duanestorey/hifi-amp-pcbs/pcbs/_ready/lift/readme.md

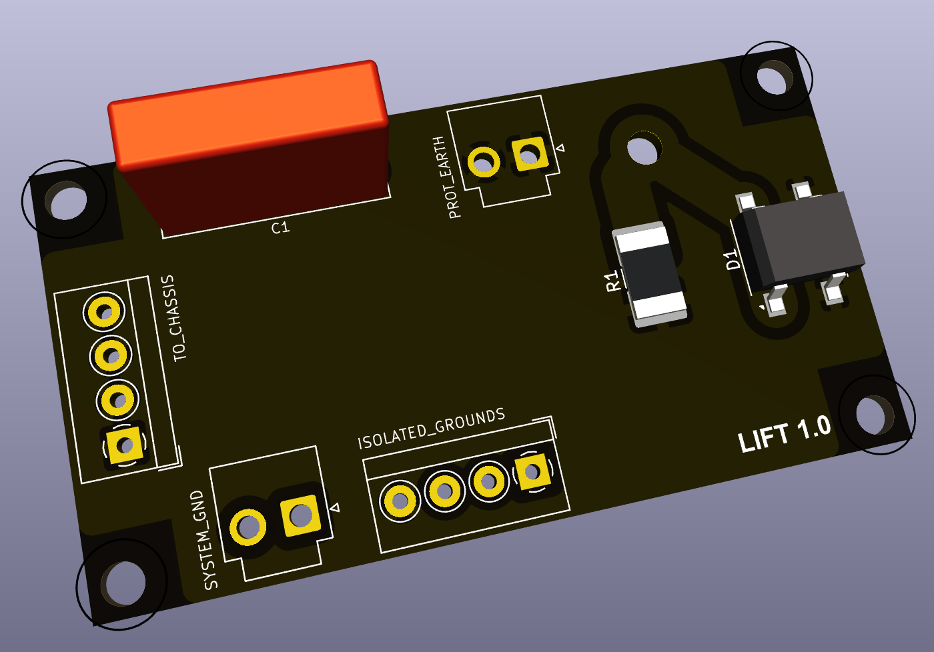
[picture p11: pcbs/_Ready/Lift/screenshot.png]


## Ground Lift

This board provides a ground-lift circuit to isolate the audio grounds from the chassis ground.  May not be legal in some juridictions, but should be safe.

### Version History

- 1.0: Initial Release

### Speciality Components
