duanestorey/hifi-amp-pcbs/pcbs/_ready/lift/1.0/lift.kicad_pcb

## KiCad design pcbs/_ready/lift/1.0/lift.kicad_pcb (2025-01-12)

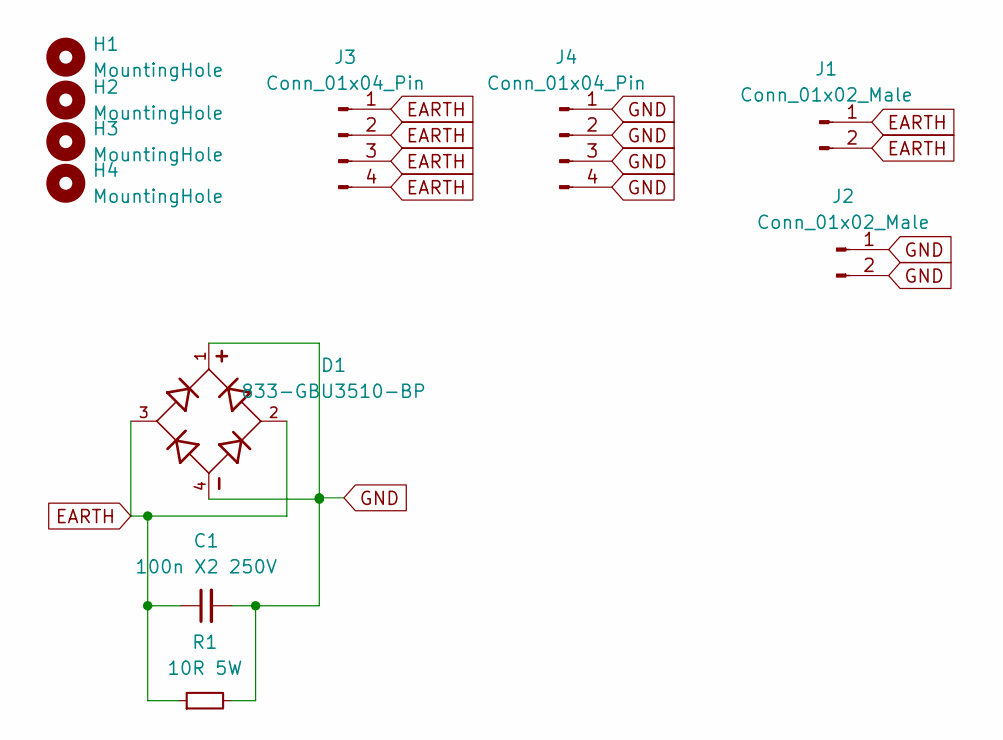
[picture p44: schematic lift.kicad_sch]

Parts:
C1: 100n X2 250V; C_Rect_L18.0mm_W5.0mm_P15.00mm_FKS3_FKP3; Mouser 871-B32922X2104K000
D1: 833-GBU3510-BP; Diode_Bridge_Vishay_GBU; Mouser 833-GBU3510-BP
H1, H2, H3, H4: MountingHole; MountingHole_3.2mm_M3_DIN965_Pad_TopOnly
J1, J2: Conn_01x02_Male; JST_VH_B2P-VH-B_1x02_P3.96mm_Vertical
J3, J4: Conn_01x04_Pin; TerminalBlock_Phoenix_PT-1,5-4-3.5-H_1x04_P3.50mm_Horizontal
R1: 10R 5W; R_Axial_DIN0617_L17.0mm_D6.0mm_P25.40mm_Horizontal; Mouser 594-AC05W10R00J

Connections:
EARTH: C1.1, D1.2, D1.3, J1.1, J1.2, J3.1, J3.2, J3.3, J3.4, R1.1
GND: C1.2, D1.1, D1.4, J2.1, J2.2, J4.1, J4.2, J4.3, J4.4, R1.2

Board: 2 copper layers, 11 parts (0 on the bottom side), 2 nets, no tracks yet.
