duanestorey/hifi-amp-pcbs/pcbs/_ready/inputs/1.0/inputs.kicad_pcb

## KiCad design pcbs/_ready/inputs/1.0/inputs.kicad_pcb (2025-01-12)

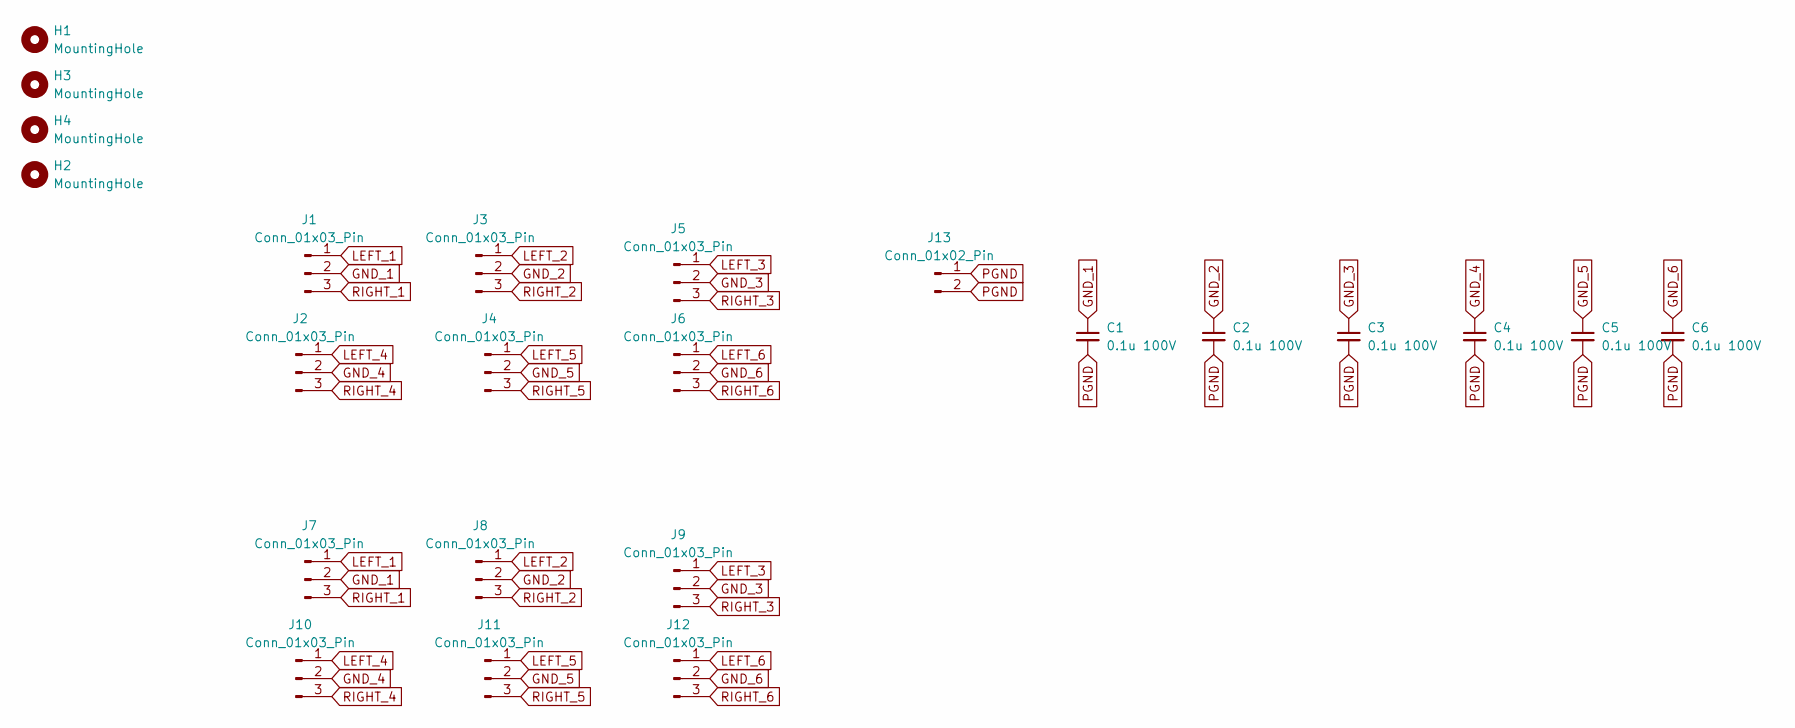
[picture p45: schematic inputs.kicad_sch]

Parts:
C1, C2, C3, C4, C5, C6: 0.1u 100V; C_1206_3216Metric; Mouser 791-1206B104K101CT
H1, H2, H3, H4: MountingHole; MountingHole_3.2mm_M3_DIN965_Pad_TopOnly
J1, J2, J3, J4, J5, J6, J7, J8, J9, J10, J11, J12: Conn_01x03_Pin; JST_PH_B3B-PH-K_1x03_P2.00mm_Vertical
J13: Conn_01x02_Pin; JST_VH_B2P-VH-B_1x02_P3.96mm_Vertical

Connections:
GND_1: C1.1, J1.2, J7.2
GND_2: C2.1, J3.2, J8.2
GND_3: C3.1, J5.2, J9.2
GND_4: C4.1, J2.2, J10.2
GND_5: C5.1, J4.2, J11.2
GND_6: C6.1, J6.2, J12.2
LEFT_1: J1.1, J7.1
LEFT_2: J3.1, J8.1
LEFT_3: J5.1, J9.1
LEFT_4: J2.1, J10.1
LEFT_5: J4.1, J11.1
LEFT_6: J6.1, J12.1
PGND: C1.2, C2.2, C3.2, C4.2, C5.2, C6.2, J13.1, J13.2
RIGHT_1: J1.3, J7.3
RIGHT_2: J3.3, J8.3
RIGHT_3: J5.3, J9.3
RIGHT_4: J2.3, J10.3
RIGHT_5: J4.3, J11.3
RIGHT_6: J6.3, J12.3

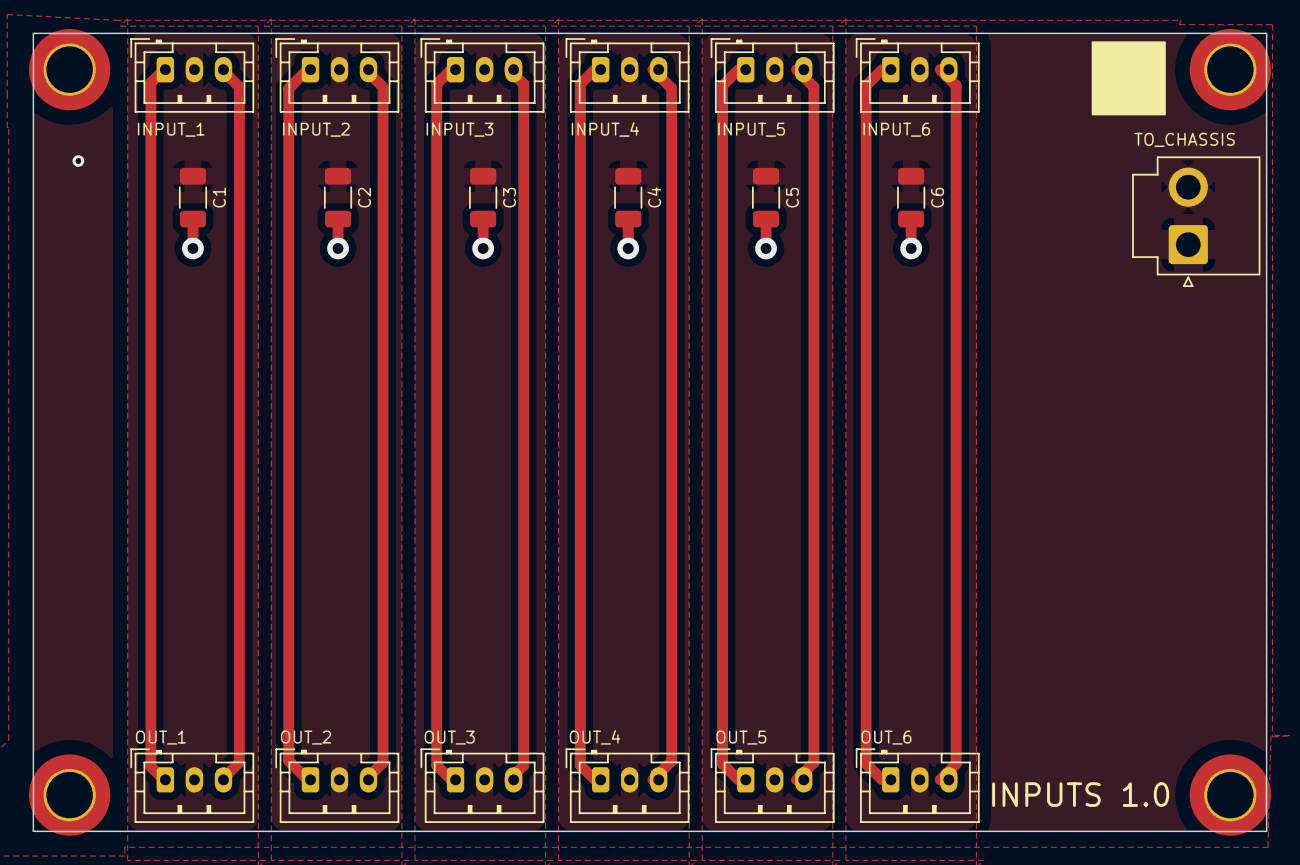
[picture p46: board inputs.kicad_pcb from above]

Board: 2 copper layers, 85.0 x 55.0 mm, 23 parts (0 on the bottom side), 19 nets.
