duanestorey/hifi-amp-pcbs/pcbs/_ready/extend/1.0/extend.kicad_pcb

## KiCad design pcbs/_ready/extend/1.0/extend.kicad_pcb (2025-01-12)

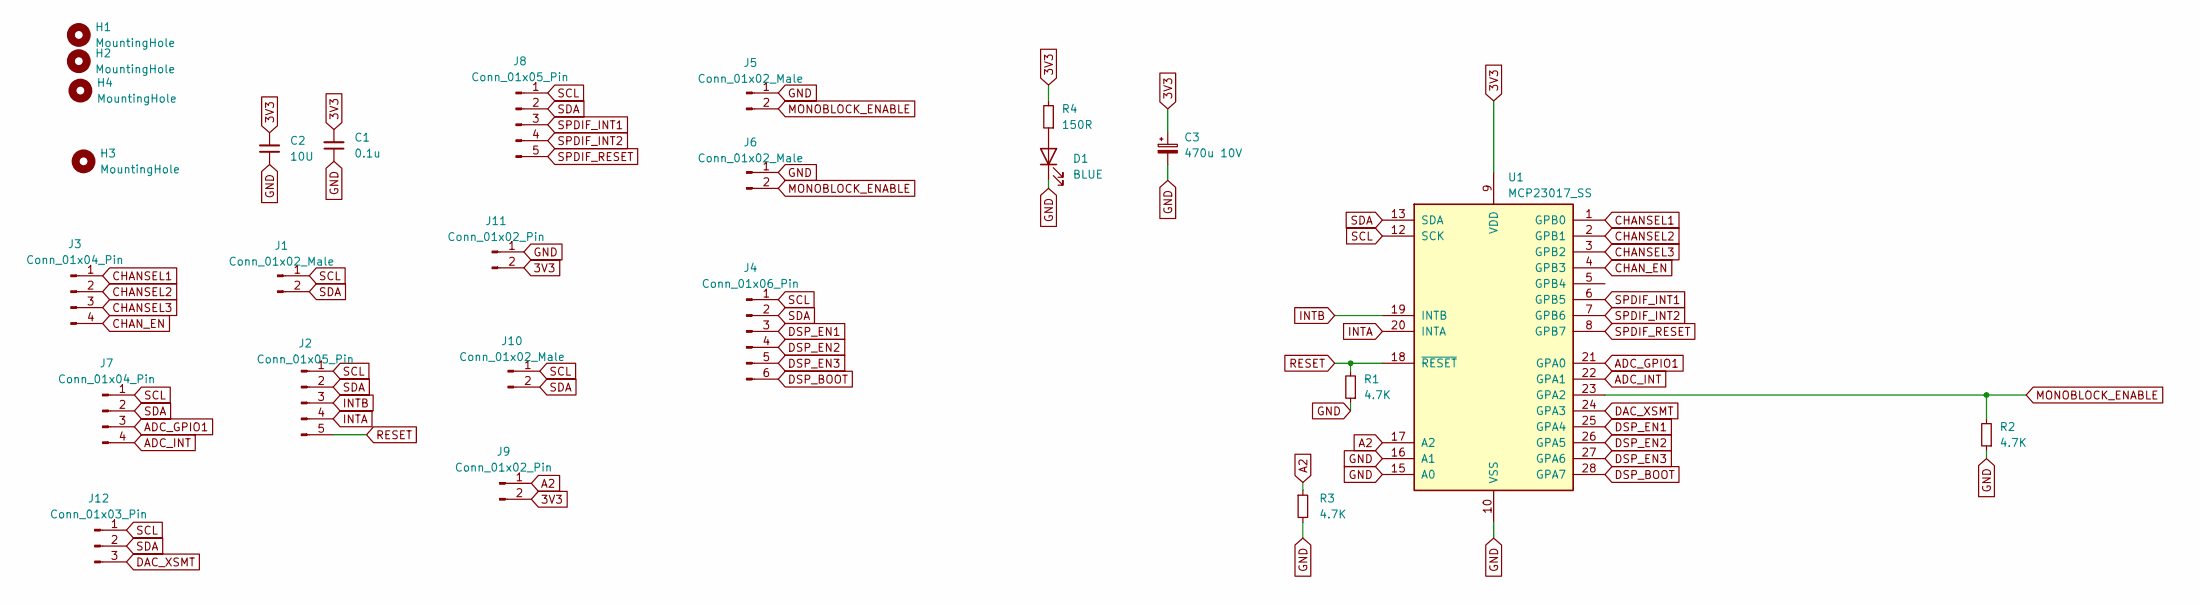
[picture p47: schematic extend.kicad_sch]

Parts:
C1: 0.1u; C_0805_2012Metric_Pad1.18x1.45mm_HandSolder
C2: 10U; C_1206_3216Metric_Pad1.33x1.80mm_HandSolder
C3: 470u 10V; CP_Radial_D6.3mm_P2.50mm
D1: BLUE; LED_0603_1608Metric
H1, H2, H3, H4: MountingHole; MountingHole_3.2mm_M3_DIN965_Pad_TopOnly
J1, J5, J6, J10: Conn_01x02_Male; JST_PH_B2B-PH-K_1x02_P2.00mm_Vertical
J2, J8: Conn_01x05_Pin; JST_PH_B5B-PH-K_1x05_P2.00mm_Vertical
J3, J7: Conn_01x04_Pin; JST_PH_B4B-PH-K_1x04_P2.00mm_Vertical
J4: Conn_01x06_Pin; JST_PH_B6B-PH-K_1x06_P2.00mm_Vertical
J9: Conn_01x02_Pin; PinHeader_1x02_P2.54mm_Vertical
J11: Conn_01x02_Pin; JST_PH_B2B-PH-K_1x02_P2.00mm_Vertical
J12: Conn_01x03_Pin; JST_PH_B3B-PH-K_1x03_P2.00mm_Vertical
R1, R2, R3: 4.7K; R_0603_1608Metric_Pad0.98x0.95mm_HandSolder
R4: 150R; R_0603_1608Metric
U1: MCP23017_SS; SSOP-28_5.3x10.2mm_P0.65mm; Mouser 579-MCP23017-E/SS

Connections:
3V3: C1.2, C2.2, C3.1, J9.2, J11.2, R4.2, U1.9 (VDD)
A2: J9.1, R3.1, U1.17 (A2)
ADC_GPIO1: J7.3, U1.21 (GPA0)
ADC_INT: J7.4, U1.22 (GPA1)
CHANSEL1: J3.1, U1.1 (GPB0)
CHANSEL2: J3.2, U1.2 (GPB1)
CHANSEL3: J3.3, U1.3 (GPB2)
CHAN_EN: J3.4, U1.4 (GPB3)
DAC_XSMT: J12.3, U1.24 (GPA3)
DSP_BOOT: J4.6, U1.28 (GPA7)
DSP_EN1: J4.3, U1.25 (GPA4)
DSP_EN2: J4.4, U1.26 (GPA5)
DSP_EN3: J4.5, U1.27 (GPA6)
GND: C1.1, C2.1, C3.2, D1.1 (K), J5.1, J6.1, J11.1, R1.1, R2.1, R3.2, U1.10 (VSS), U1.15 (A0), U1.16 (A1)
INTA: J2.4, U1.20 (INTA)
INTB: J2.3, U1.19 (INTB)
MONOBLOCK_ENABLE: J5.2, J6.2, R2.2, U1.23 (GPA2)
unnamed: D1.2 (A), R4.1
RESET: J2.5, R1.2, U1.18 (~RESET)
SCL: J1.1, J2.1, J4.1, J7.1, J8.1, J10.1, J12.1, U1.12 (SCK)
SDA: J1.2, J2.2, J4.2, J7.2, J8.2, J10.2, J12.2, U1.13 (SDA)
SPDIF_INT1: J8.3, U1.6 (GPB5)
SPDIF_INT2: J8.4, U1.7 (GPB6)
SPDIF_RESET: J8.5, U1.8 (GPB7)

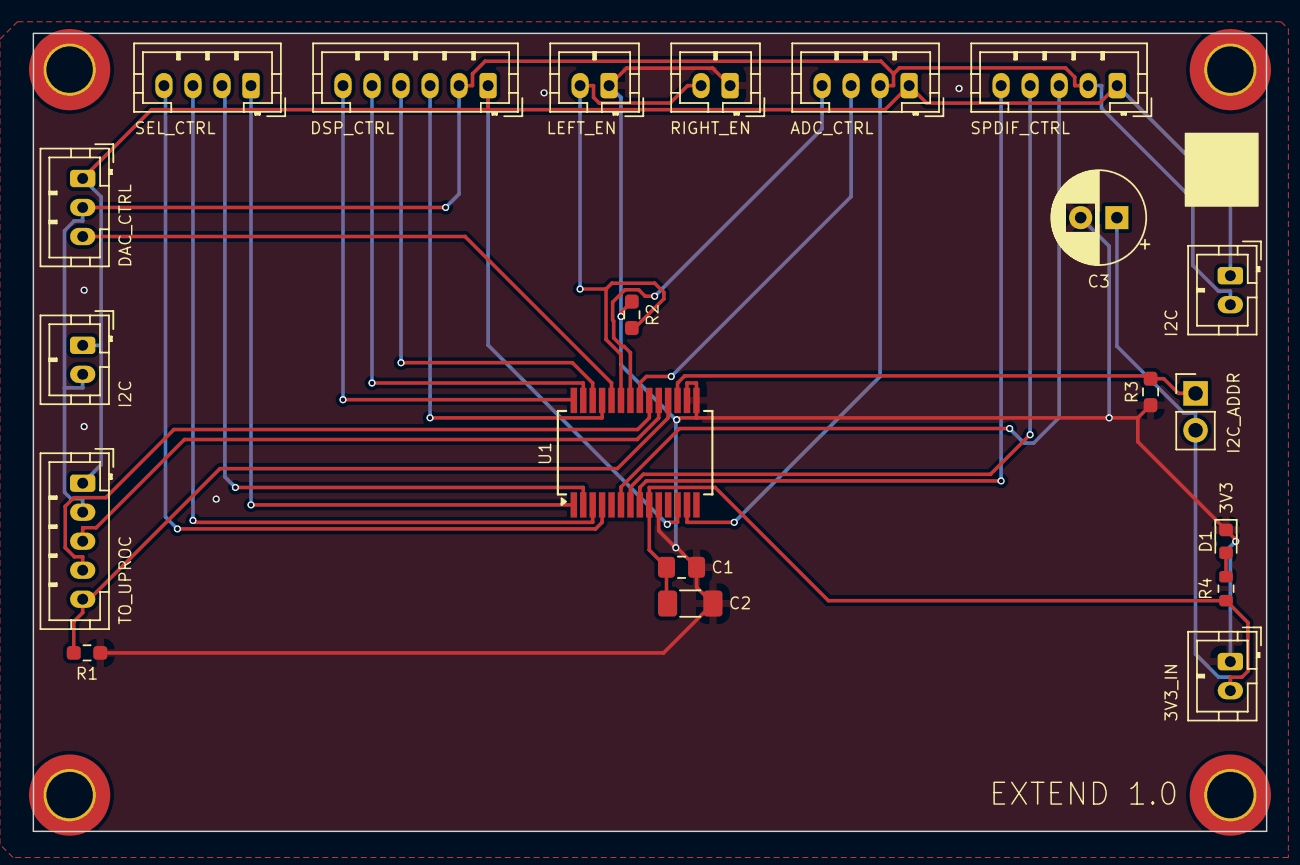
[picture p48: board extend.kicad_pcb from above]

Board: 2 copper layers, 85.0 x 55.0 mm, 25 parts (0 on the bottom side), 24 nets.
