duanestorey/hifi-amp-pcbs/pcbs/_ready/dac/1.0/dac.kicad_pcb

## KiCad design pcbs/_ready/dac/1.0/dac.kicad_pcb (2025-01-12)

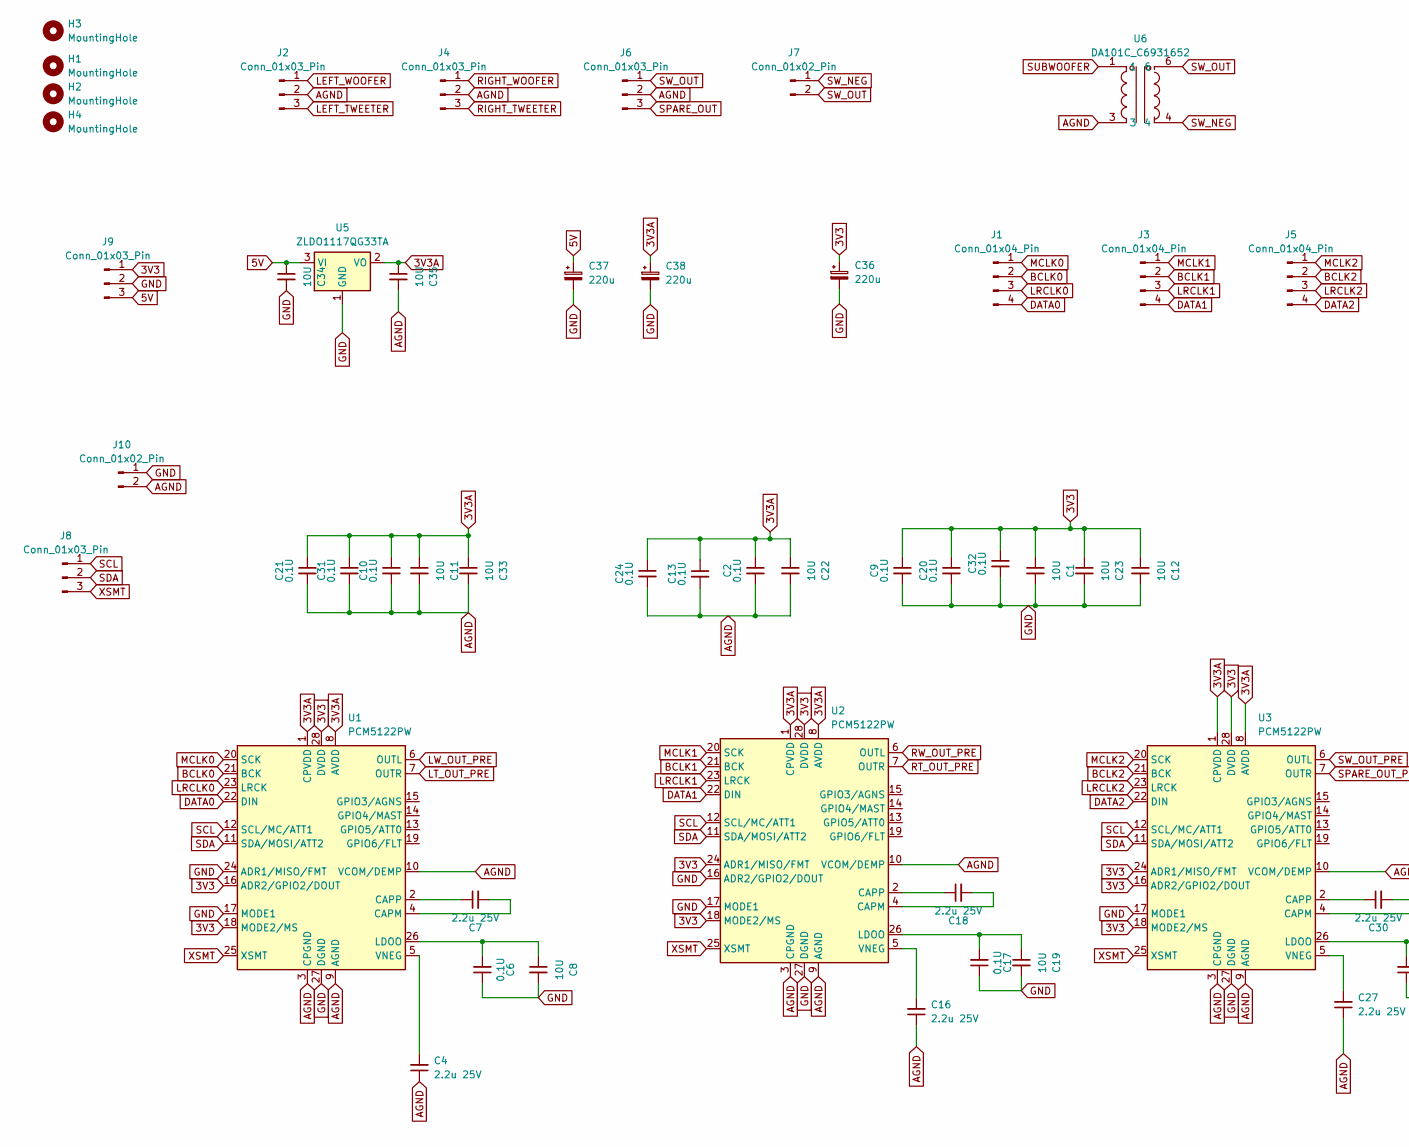
[picture p49: schematic dac.kicad_sch, part in row 1, column 1]

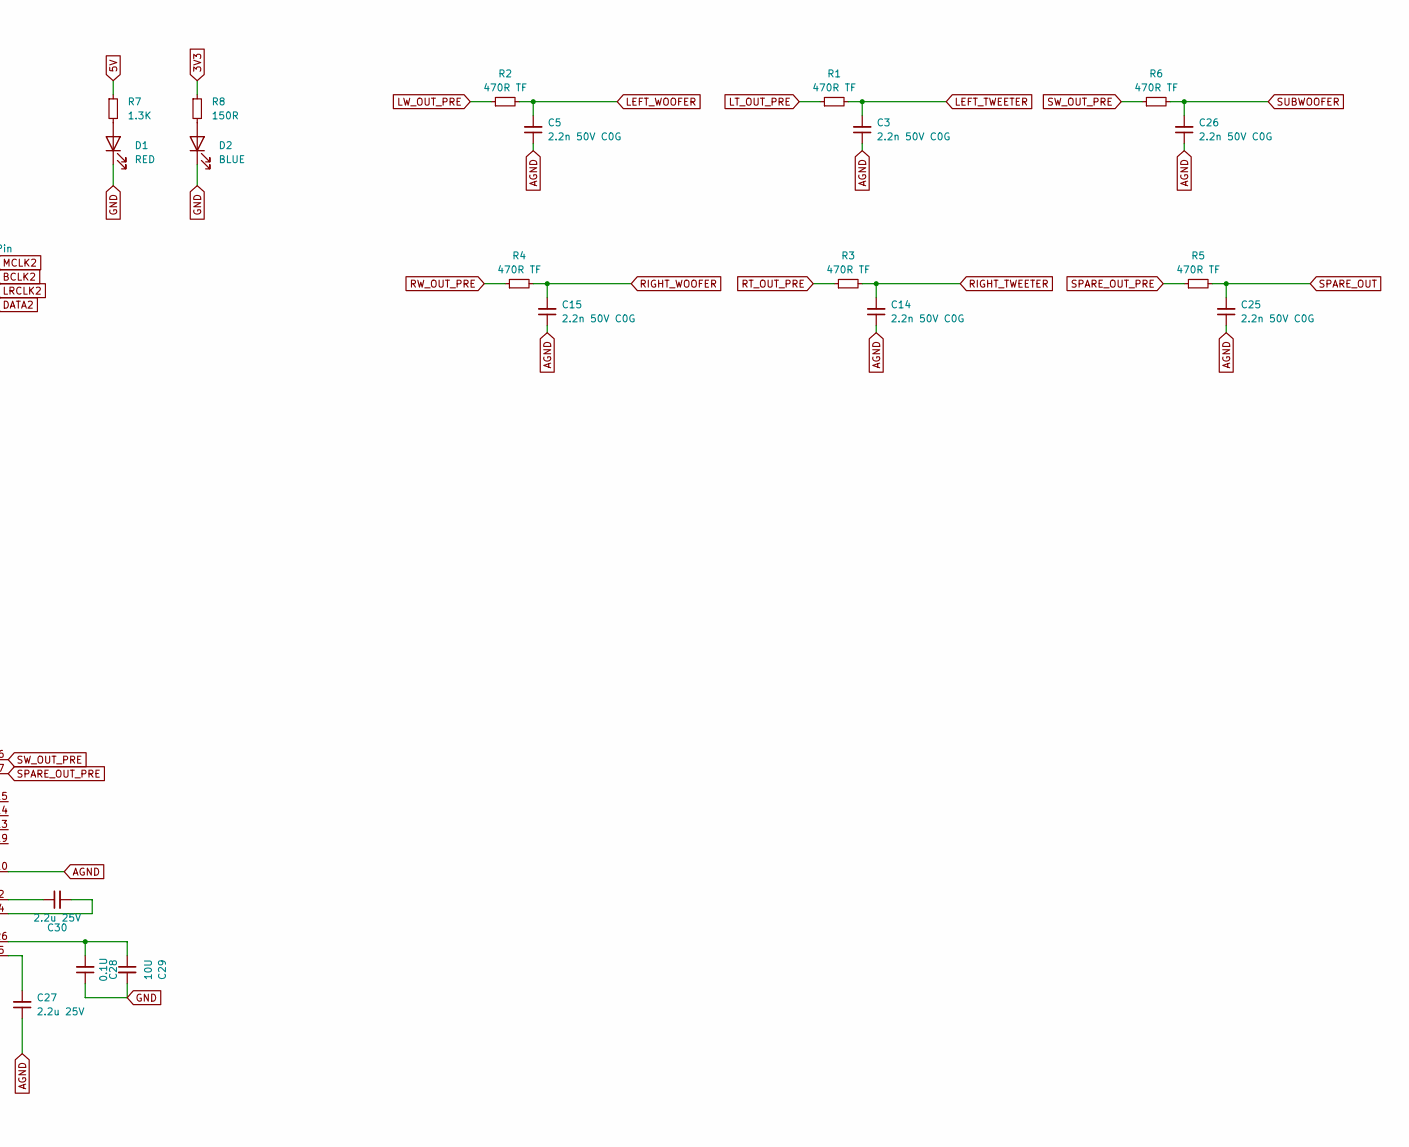
[picture p50: schematic dac.kicad_sch, part in row 1, column 2]

Parts:
C1, C8, C11, C12, C19, C22, C23, C29, C33, C34, C35: 10U; C_1206_3216Metric_Pad1.33x1.80mm_HandSolder
C2, C6, C9, C10, C13, C17, C20, C21, C24, C28, C31, C32: 0.1U; C_0805_2012Metric_Pad1.18x1.45mm_HandSolder
C3, C5, C14, C15: 2.2n 50V C0G; C_0805_2012Metric_Pad1.18x1.45mm_HandSolder; Mouser 791-0805N222F500CT
C4, C16, C27: 2.2u 25V; C_1206_3216Metric_Pad1.33x1.80mm_HandSolder; Mouser 603-CC1206JKX78BB225
C7, C18, C30: 2.2u 25V; C_0805_2012Metric_Pad1.18x1.45mm_HandSolder; Mouser 603-CC1206JKX78BB225
C25, C26: 2.2n 50V C0G; C_0805_2012Metric_Pad1.18x1.45mm_HandSolder
C36, C37, C38: 220u; CP_Radial_D6.3mm_P2.50mm
D1: RED; LED_0603_1608Metric
D2: BLUE; LED_0603_1608Metric
H1, H2, H3, H4: MountingHole; MountingHole_3.2mm_M3_DIN965_Pad_TopOnly
J1, J3, J5: Conn_01x04_Pin; JST_PH_B4B-PH-K_1x04_P2.00mm_Vertical
J2, J4, J6, J8, J9: Conn_01x03_Pin; JST_PH_B3B-PH-K_1x03_P2.00mm_Vertical
J7: Conn_01x02_Pin; JST_PH_B2B-PH-K_1x02_P2.00mm_Vertical
J10: Conn_01x02_Pin; PinHeader_1x02_P2.54mm_Vertical
R1, R2, R3, R4, R5, R6: 470R TF; R_0805_2012Metric_Pad1.20x1.40mm_HandSolder; Mouser 603-RT0805FRE07470RL
R7: 1.3K; R_0603_1608Metric_Pad0.98x0.95mm_HandSolder
R8: 150R; R_0603_1608Metric_Pad0.98x0.95mm_HandSolder
U1, U2, U3: PCM5122PW; TSSOP-28_4.4x9.7mm_P0.65mm; Mouser 595-PCM5122PWR
U5: ZLDO1117QG33TA; SOT-223-3_TabPin2
U6: DA101C_C6931652; XFMR-TH_4P-L9.5-W9.0-P5.08-LS10.2_C9900096976; LCSC Part C6931652

Connections:
3V3: C1.1, C9.1, C12.1, C20.1, C23.1, C32.1, C36.1, J9.1, R8.1, U1.16 (ADR2/GPIO2/DOUT), U1.18 (MODE2/MS), U1.28 (DVDD), U2.18 (MODE2/MS), U2.24 (ADR1/MISO/FMT), U2.28 (DVDD), U3.16 (ADR2/GPIO2/DOUT), U3.18 (MODE2/MS), U3.24 (ADR1/MISO/FMT), U3.28 (DVDD)
3V3A: C2.1, C10.1, C11.1, C13.1, C21.1, C22.1, C24.1, C31.1, C33.1, C35.1, C38.1, U1.1 (CPVDD), U1.8 (AVDD), U2.1 (CPVDD), U2.8 (AVDD), U3.1 (CPVDD), U3.8 (AVDD), U5.2 (VO)
5V: C34.1, C37.1, J9.3, R7.1, U5.3 (VI)
AGND: C2.2, C3.1, C4.1, C5.1, C10.2, C11.2, C13.2, C14.1, C15.1, C16.1, C21.2, C22.2, C24.2, C25.1, C26.1, C27.1, C31.2, C33.2, C35.2, J2.2, J4.2, J6.2, J10.2, U1.3 (CPGND), U1.9 (AGND), U1.10 (VCOM/DEMP), U2.3 (CPGND), U2.9 (AGND), U2.10 (VCOM/DEMP), U3.3 (CPGND), U3.9 (AGND), U3.10 (VCOM/DEMP), U6.3
BCLK0: J1.2, U1.21 (BCK)
BCLK1: J3.2, U2.21 (BCK)
BCLK2: J5.2, U3.21 (BCK)
DATA0: J1.4, U1.22 (DIN)
DATA1: J3.4, U2.22 (DIN)
DATA2: J5.4, U3.22 (DIN)
GND: C1.2, C6.1, C8.2, C9.2, C12.2, C17.1, C19.2, C20.2, C23.2, C28.1, C29.2, C32.2, C34.2, C36.2, C37.2, C38.2, D1.1 (K), D2.1 (K), J9.2, J10.1, U1.17 (MODE1), U1.24 (ADR1/MISO/FMT), U1.27 (DGND), U2.16 (ADR2/GPIO2/DOUT), U2.17 (MODE1), U2.27 (DGND), U3.17 (MODE1), U3.27 (DGND), U5.1 (GND)
LEFT_TWEETER: C3.2, J2.3, R1.2
LEFT_WOOFER: C5.2, J2.1, R2.2
LRCLK0: J1.3, U1.23 (LRCK)
LRCLK1: J3.3, U2.23 (LRCK)
LRCLK2: J5.3, U3.23 (LRCK)
LT_OUT_PRE: R1.1, U1.7 (OUTR)
LW_OUT_PRE: R2.1, U1.6 (OUTL)
MCLK0: J1.1, U1.20 (SCK)
MCLK1: J3.1, U2.20 (SCK)
MCLK2: J5.1, U3.20 (SCK)
unnamed: D1.2 (A), R7.2
unnamed: D2.2 (A), R8.2
unnamed: C7.2, U1.4 (CAPM)
unnamed: C7.1, U1.2 (CAPP)
unnamed: C6.2, C8.1, U1.26 (LDOO)
unnamed: C4.2, U1.5 (VNEG)
unnamed: C18.2, U2.4 (CAPM)
unnamed: C18.1, U2.2 (CAPP)
unnamed: C17.2, C19.1, U2.26 (LDOO)
unnamed: C16.2, U2.5 (VNEG)
unnamed: C30.2, U3.4 (CAPM)
unnamed: C30.1, U3.2 (CAPP)
unnamed: C28.2, C29.1, U3.26 (LDOO)
unnamed: C27.2, U3.5 (VNEG)
RIGHT_TWEETER: C14.2, J4.3, R3.2
RIGHT_WOOFER: C15.2, J4.1, R4.2
RT_OUT_PRE: R3.1, U2.7 (OUTR)
RW_OUT_PRE: R4.1, U2.6 (OUTL)
SCL: J8.1, U1.12 (SCL/MC/ATT1), U2.12 (SCL/MC/ATT1), U3.12 (SCL/MC/ATT1)
SDA: J8.2, U1.11 (SDA/MOSI/ATT2), U2.11 (SDA/MOSI/ATT2), U3.11 (SDA/MOSI/ATT2)
SPARE_OUT: C25.2, J6.3, R5.2
SPARE_OUT_PRE: R5.1, U3.7 (OUTR)
SUBWOOFER: C26.2, R6.2, U6.1
SW_NEG: J7.1, U6.4
SW_OUT: J6.1, J7.2, U6.6
SW_OUT_PRE: R6.1, U3.6 (OUTL)
XSMT: J8.3, U1.25 (XSMT), U2.25 (XSMT), U3.25 (XSMT)

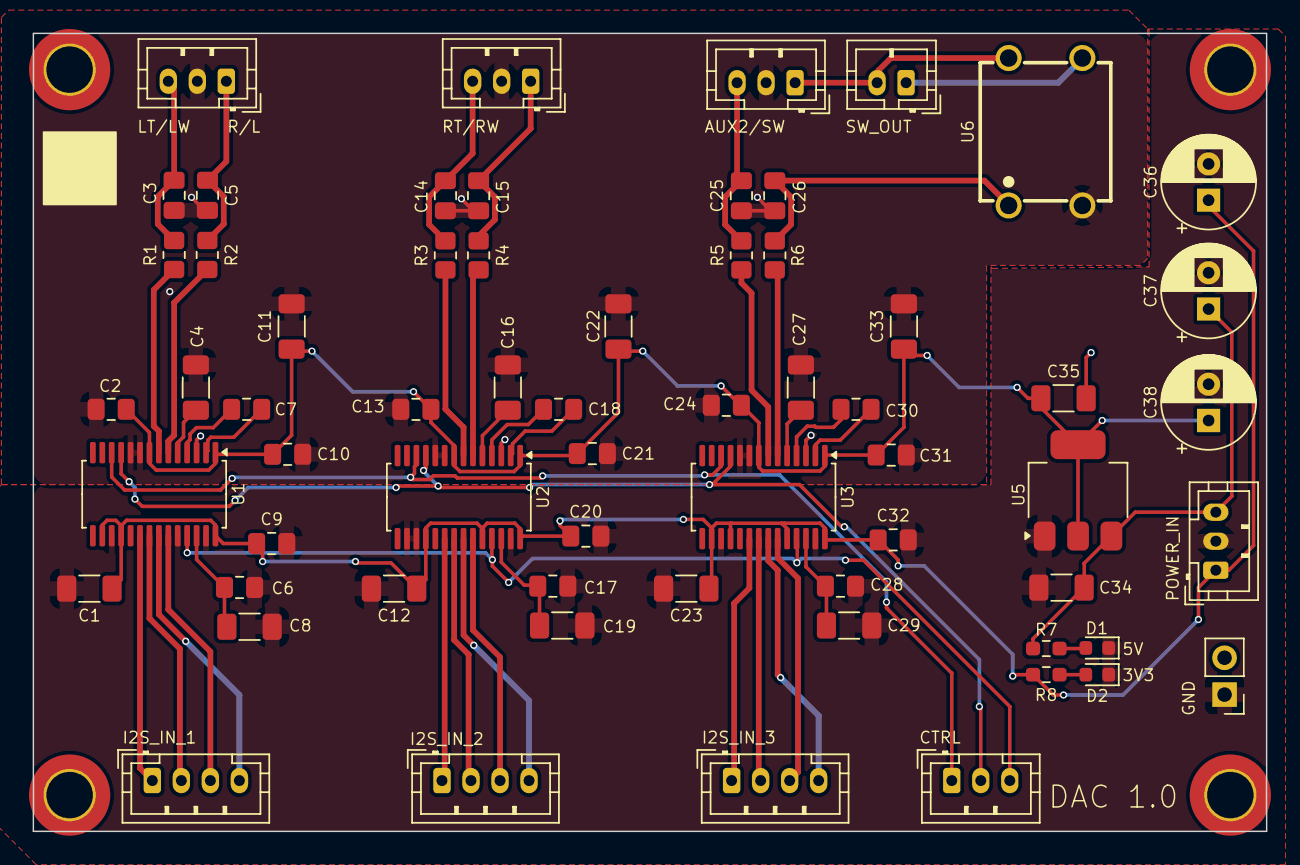
[picture p51: board dac.kicad_pcb from above]

Board: 2 copper layers, 85.0 x 55.0 mm, 67 parts (0 on the bottom side), 48 nets.
