duanestorey/hifi-amp-pcbs/pcbs/_ready/dsp/1.0/dsp.kicad_pcb

## KiCad design pcbs/_ready/dsp/1.0/dsp.kicad_pcb (2025-01-12)

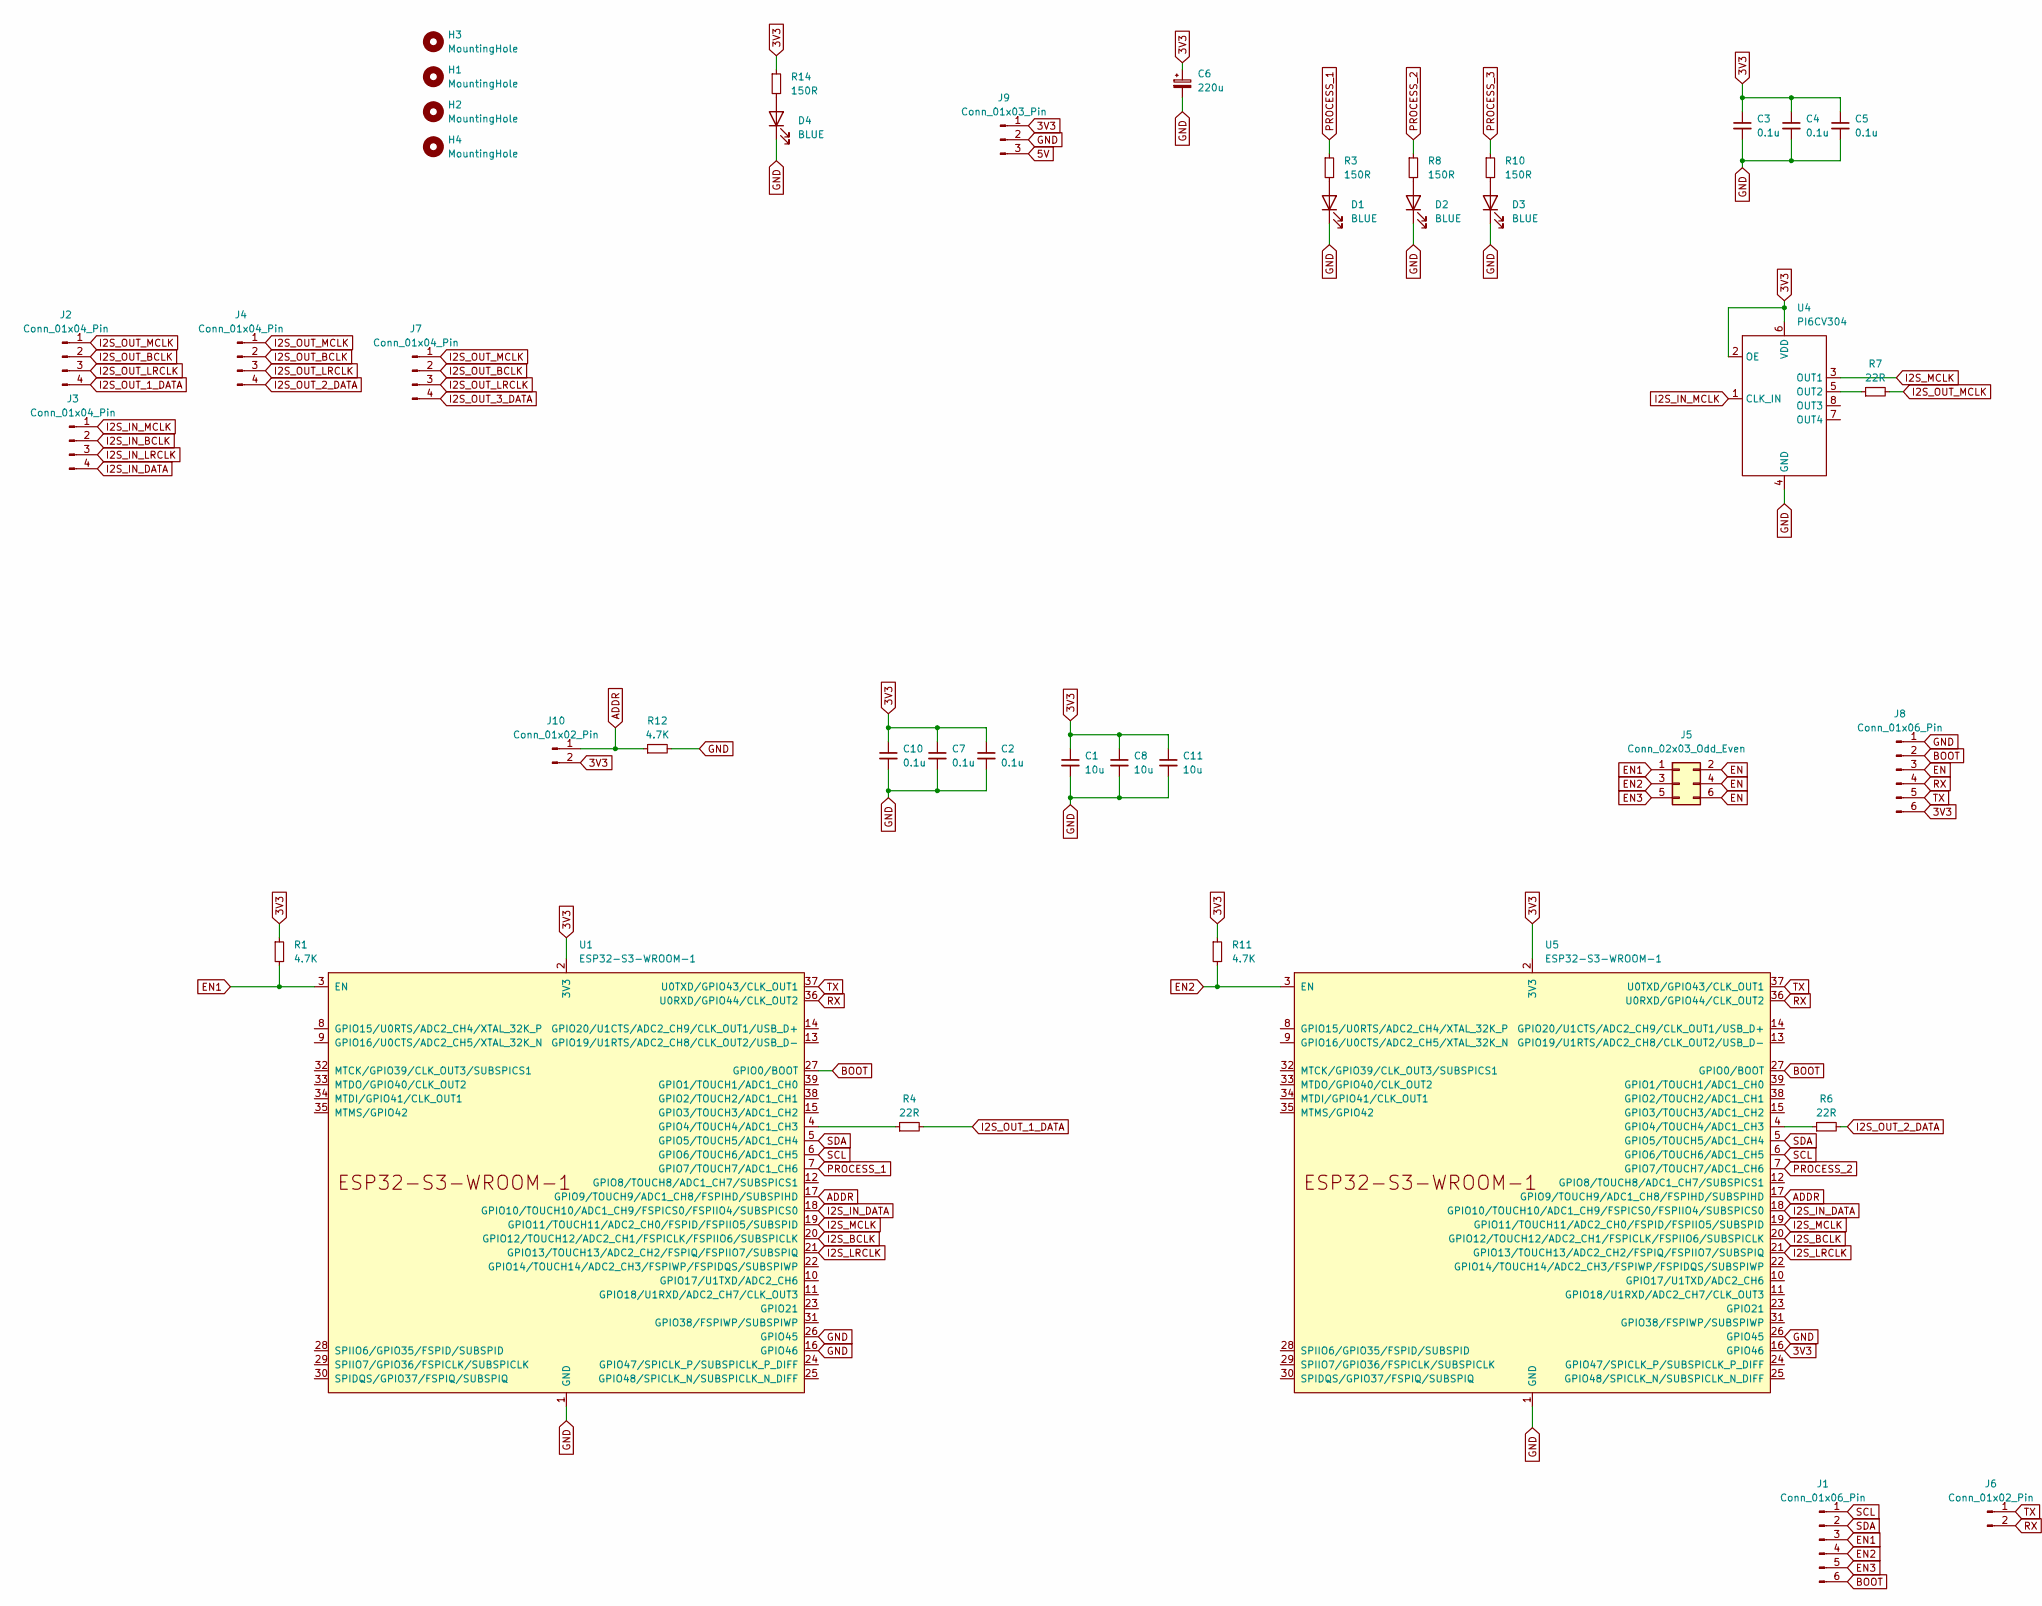
[picture p52: schematic dsp.kicad_sch, part in row 1, column 1]

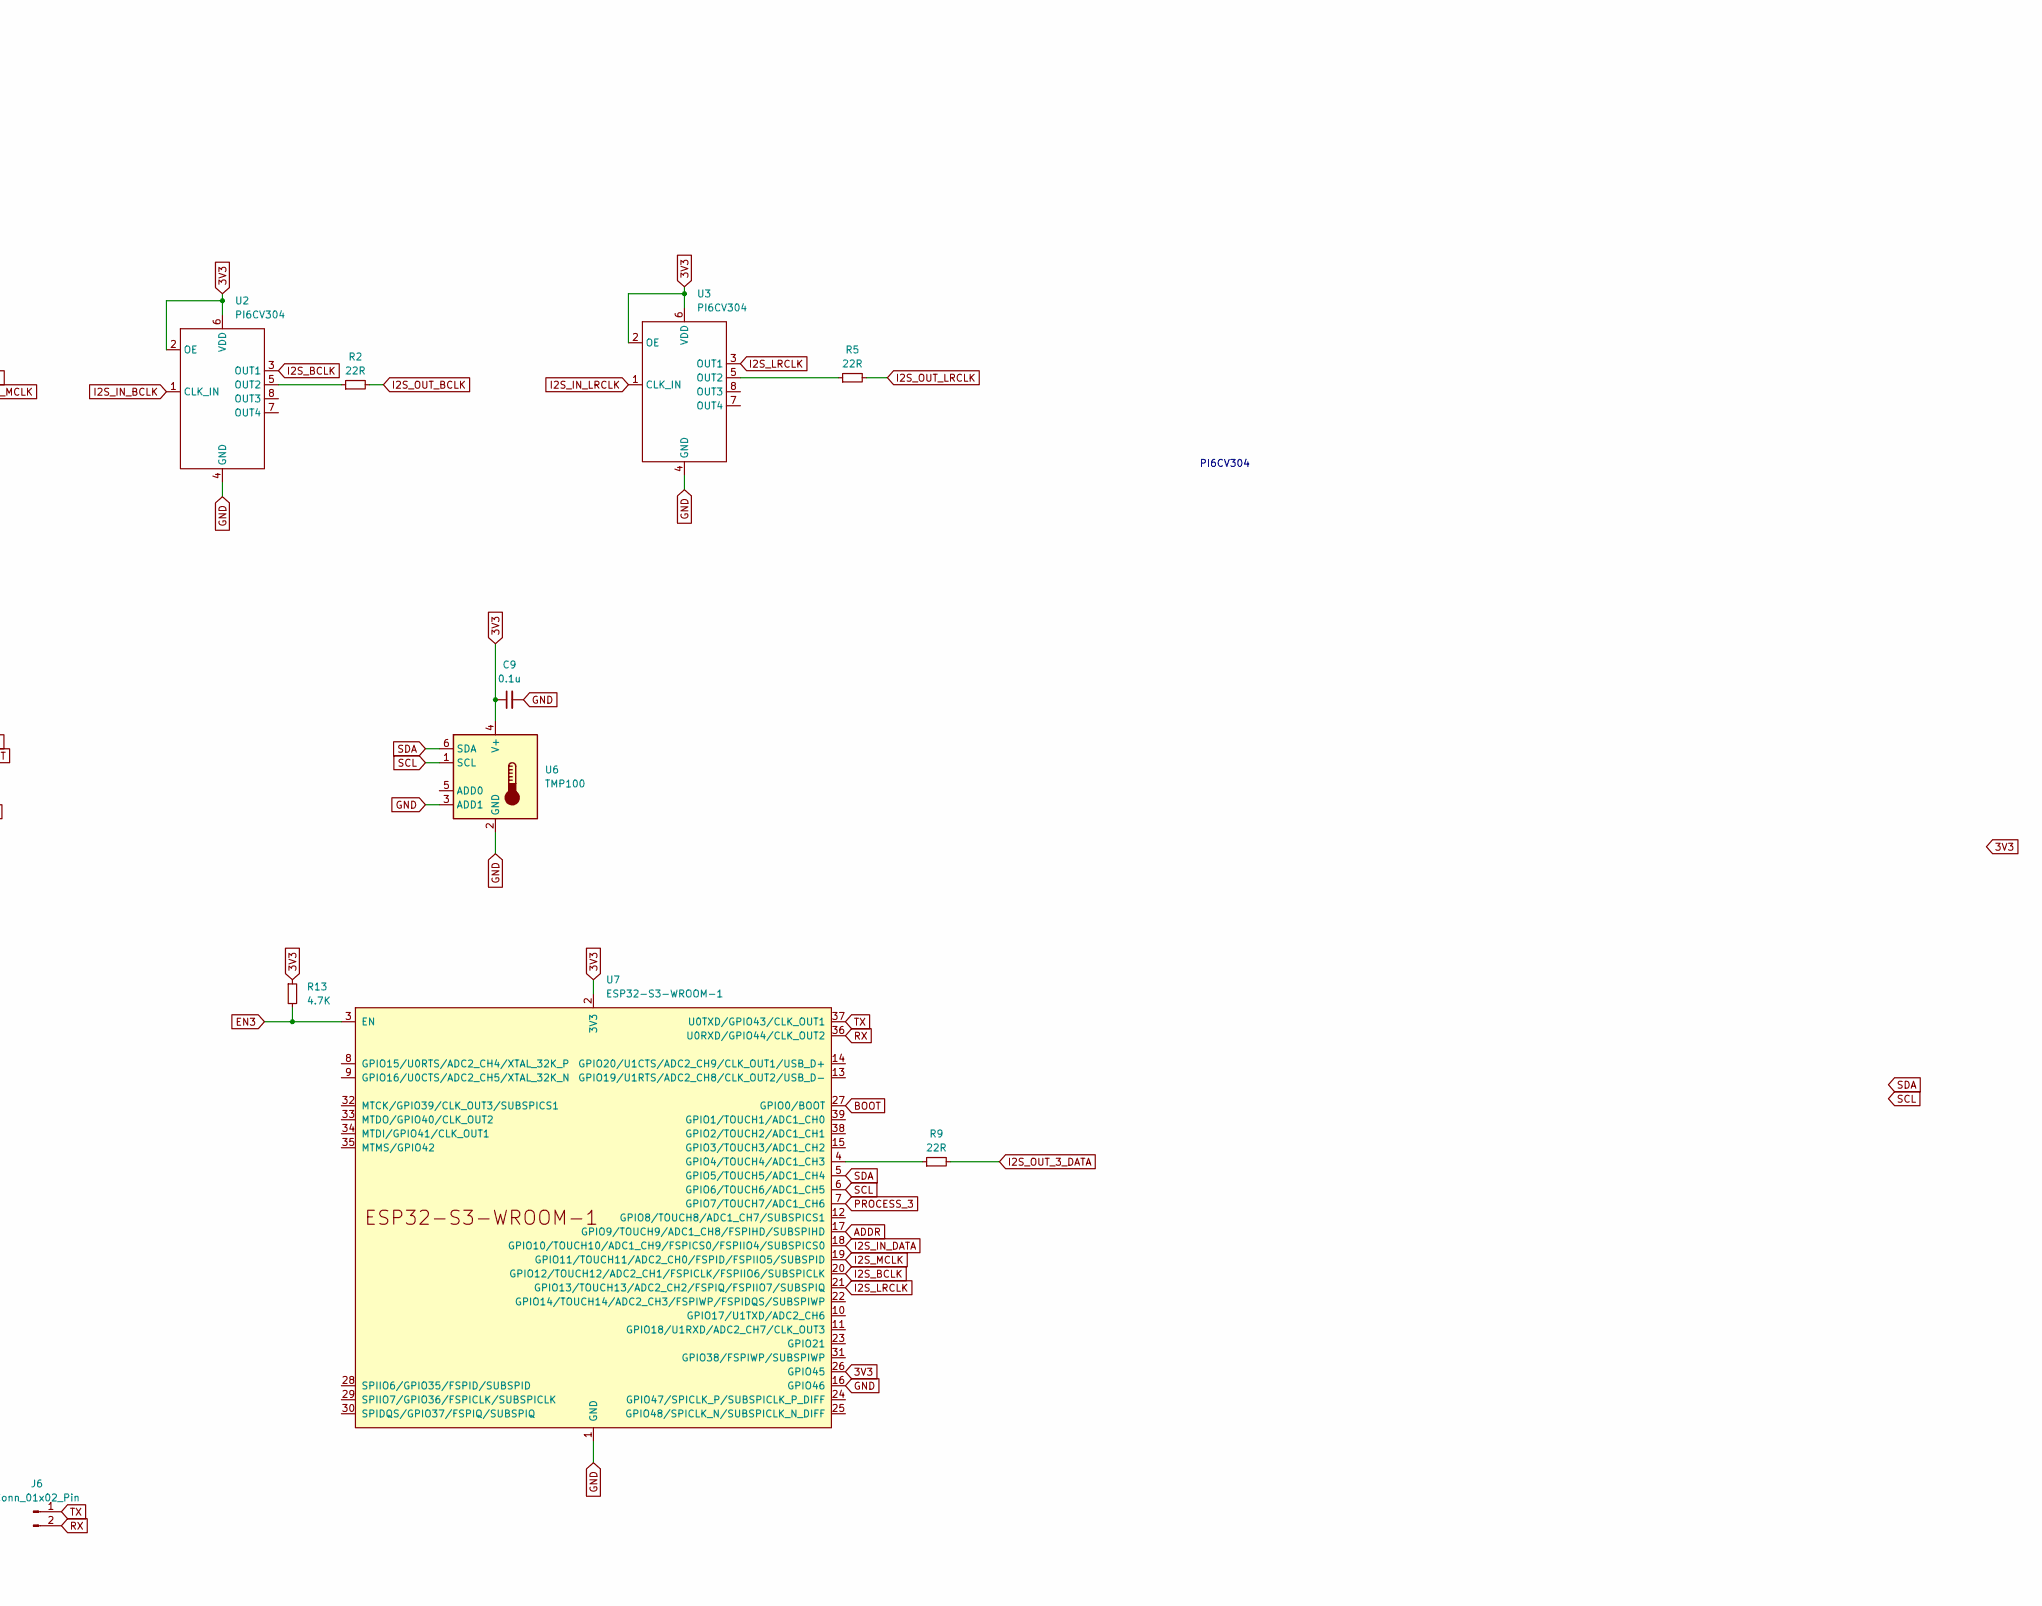
[picture p53: schematic dsp.kicad_sch, part in row 1, column 2]

Parts:
C1, C8, C11: 10u; C_0805_2012Metric_Pad1.18x1.45mm_HandSolder
C2, C3, C4, C5, C7, C9, C10: 0.1u; C_0603_1608Metric_Pad1.08x0.95mm_HandSolder
C6: 220u; CP_Radial_D6.3mm_P2.50mm; LCSC C4747974
D1, D2, D3, D4: BLUE; D_0603_1608Metric; LCSC C84259
H1, H2, H3, H4: MountingHole; MountingHole_3.2mm_M3_DIN965_Pad_TopOnly
J1: Conn_01x06_Pin; JST_PH_B6B-PH-K_1x06_P2.00mm_Vertical
J2, J3, J4, J7: Conn_01x04_Pin; JST_PH_B4B-PH-K_1x04_P2.00mm_Vertical
J5: Conn_02x03_Odd_Even; PinHeader_2x03_P2.54mm_Vertical
J6: Conn_01x02_Pin; JST_PH_B2B-PH-K_1x02_P2.00mm_Vertical
J8: Conn_01x06_Pin; PinHeader_1x06_P2.54mm_Vertical
J9: Conn_01x03_Pin; JST_PH_B3B-PH-K_1x03_P2.00mm_Vertical
J10: Conn_01x02_Pin; PinHeader_1x02_P2.54mm_Vertical
R1, R11, R12, R13: 4.7K; R_0603_1608Metric; LCSC C23162
R2, R5, R7: 22R; R_0603_1608Metric
R3, R8, R10, R14: 150R; R_0603_1608Metric; LCSC C22808
R4, R9: 22R; R_0805_2012Metric; Mouser 603-RT0805FRE0722RL
R6: 22R; R_0805_2012Metric
U1, U5, U7: ESP32-S3-WROOM-1; Mouser 356-ESP32S3WRM1N16R8
U2, U3, U4: PI6CV304; TSSOP-8_4.4x3mm_P0.65mm
U6: TMP100; SOT-23-6

Connections:
3V3: C1.1, C2.1, C3.1, C4.1, C5.1, C6.1, C7.1, C8.1, C9.1, C10.1, C11.1, J8.6, J9.1, J10.2, R1.1, R11.1, R13.1, R14.1, U1.2 (3V3), U2.2 (OE), U2.6 (VDD), U3.2 (OE), U3.6 (VDD), U4.2 (OE), U4.6 (VDD), U5.2 (3V3), U5.16 (GPIO46), U6.4 (V+), U7.2 (3V3), U7.26 (GPIO45)
5V: J9.3
ADDR: J10.1, R12.1, U1.17 (GPIO9/TOUCH9/ADC1_CH8/FSPIHD/SUBSPIHD), U5.17 (GPIO9/TOUCH9/ADC1_CH8/FSPIHD/SUBSPIHD), U7.17 (GPIO9/TOUCH9/ADC1_CH8/FSPIHD/SUBSPIHD)
BOOT: J1.6, J8.2, U1.27 (GPIO0/BOOT), U5.27 (GPIO0/BOOT), U7.27 (GPIO0/BOOT)
EN: J5.2, J5.4, J5.6, J8.3
EN1: J1.3, J5.1, R1.2, U1.3 (EN)
EN2: J1.4, J5.3, R11.2, U5.3 (EN)
EN3: J1.5, J5.5, R13.2, U7.3 (EN)
GND: C1.2, C2.2, C3.2, C4.2, C5.2, C6.2, C7.2, C8.2, C9.2, C10.2, C11.2, D1.1 (K), D2.1 (K), D3.1 (K), D4.1 (K), J8.1, J9.2, R12.2, U1.1 (GND), U1.16 (GPIO46), U1.26 (GPIO45), U1.40 (GND), U1.41 (GND), U2.4 (GND), U3.4 (GND), U4.4 (GND), U5.1 (GND), U5.26 (GPIO45), U5.40 (GND), U5.41 (GND), U6.2 (GND), U6.3 (ADD1), U7.1 (GND), U7.16 (GPIO46), U7.40 (GND), U7.41 (GND)
I2S_BCLK: U1.20 (GPIO12/TOUCH12/ADC2_CH1/FSPICLK/FSPIIO6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), U2.3 (OUT1), U5.20 (GPIO12/TOUCH12/ADC2_CH1/FSPICLK/FSPIIO6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), U7.20 (GPIO12/TOUCH12/ADC2_CH1/FSPICLK/FSPIIO6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)
I2S_IN_BCLK: J3.2, U2.1 (CLK_IN)
I2S_IN_DATA: J3.4, U1.18 (GPIO10/TOUCH10/ADC1_CH9/FSPICS0/FSPIIO4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), U5.18 (GPIO10/TOUCH10/ADC1_CH9/FSPICS0/FSPIIO4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), U7.18 (GPIO10/TOUCH10/ADC1_CH9/FSPICS0/FSPIIO4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)
I2S_IN_LRCLK: J3.3, U3.1 (CLK_IN)
I2S_IN_MCLK: J3.1, U4.1 (CLK_IN)
I2S_LRCLK: U1.21 (GPIO13/TOUCH13/ADC2_CH2/FSPIQ/FSPIIO7/S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), U3.3 (OUT1), U5.21 (GPIO13/TOUCH13/ADC2_CH2/FSPIQ/FSPIIO7/S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), U7.21 (GPIO13/TOUCH13/ADC2_CH2/FSPIQ/FSPIIO7/S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)
I2S_MCLK: U1.19 (GPIO11/TOUCH11/ADC2_CH0/FSPID/FSPIIO5/S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), U4.3 (OUT1), U5.19 (GPIO11/TOUCH11/ADC2_CH0/FSPID/FSPIIO5/S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), U7.19 (GPIO11/TOUCH11/ADC2_CH0/FSPID/FSPIIO5/S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)
I2S_OUT_1_DATA: J2.4, R4.2
I2S_OUT_2_DATA: J4.4, R6.2
I2S_OUT_3_DATA: J7.4, R9.2
I2S_OUT_BCLK: J2.2, J4.2, J7.2, R2.2
I2S_OUT_LRCLK: J2.3, J4.3, J7.3, R5.2
I2S_OUT_MCLK: J2.1, J4.1, J7.1, R7.2
unnamed: D1.2 (A), R3.2
unnamed: D2.2 (A), R8.2
unnamed: D3.2 (A), R10.2
unnamed: D4.2 (A), R14.2
unnamed: R4.1, U1.4 (GPIO4/TOUCH4/ADC1_CH3)
unnamed: R2.1, U2.5 (OUT2)
unnamed: R5.1, U3.5 (OUT2)
unnamed: R7.1, U4.5 (OUT2)
unnamed: R6.1, U5.4 (GPIO4/TOUCH4/ADC1_CH3)
unnamed: R9.1, U7.4 (GPIO4/TOUCH4/ADC1_CH3)
PROCESS_1: R3.1, U1.7 (GPIO7/TOUCH7/ADC1_CH6)
PROCESS_2: R8.1, U5.7 (GPIO7/TOUCH7/ADC1_CH6)
PROCESS_3: R10.1, U7.7 (GPIO7/TOUCH7/ADC1_CH6)
RX: J6.2, J8.4, U1.36 (U0RXD/GPIO44/CLK_OUT2), U5.36 (U0RXD/GPIO44/CLK_OUT2), U7.36 (U0RXD/GPIO44/CLK_OUT2)
SCL: J1.1, U1.6 (GPIO6/TOUCH6/ADC1_CH5), U5.6 (GPIO6/TOUCH6/ADC1_CH5), U6.1 (SCL), U7.6 (GPIO6/TOUCH6/ADC1_CH5)
SDA: J1.2, U1.5 (GPIO5/TOUCH5/ADC1_CH4), U5.5 (GPIO5/TOUCH5/ADC1_CH4), U6.6 (SDA), U7.5 (GPIO5/TOUCH5/ADC1_CH4)
TX: J6.1, J8.5, U1.37 (U0TXD/GPIO43/CLK_OUT1), U5.37 (U0TXD/GPIO43/CLK_OUT1), U7.37 (U0TXD/GPIO43/CLK_OUT1)

Notes on the sheet:
PI6CV304

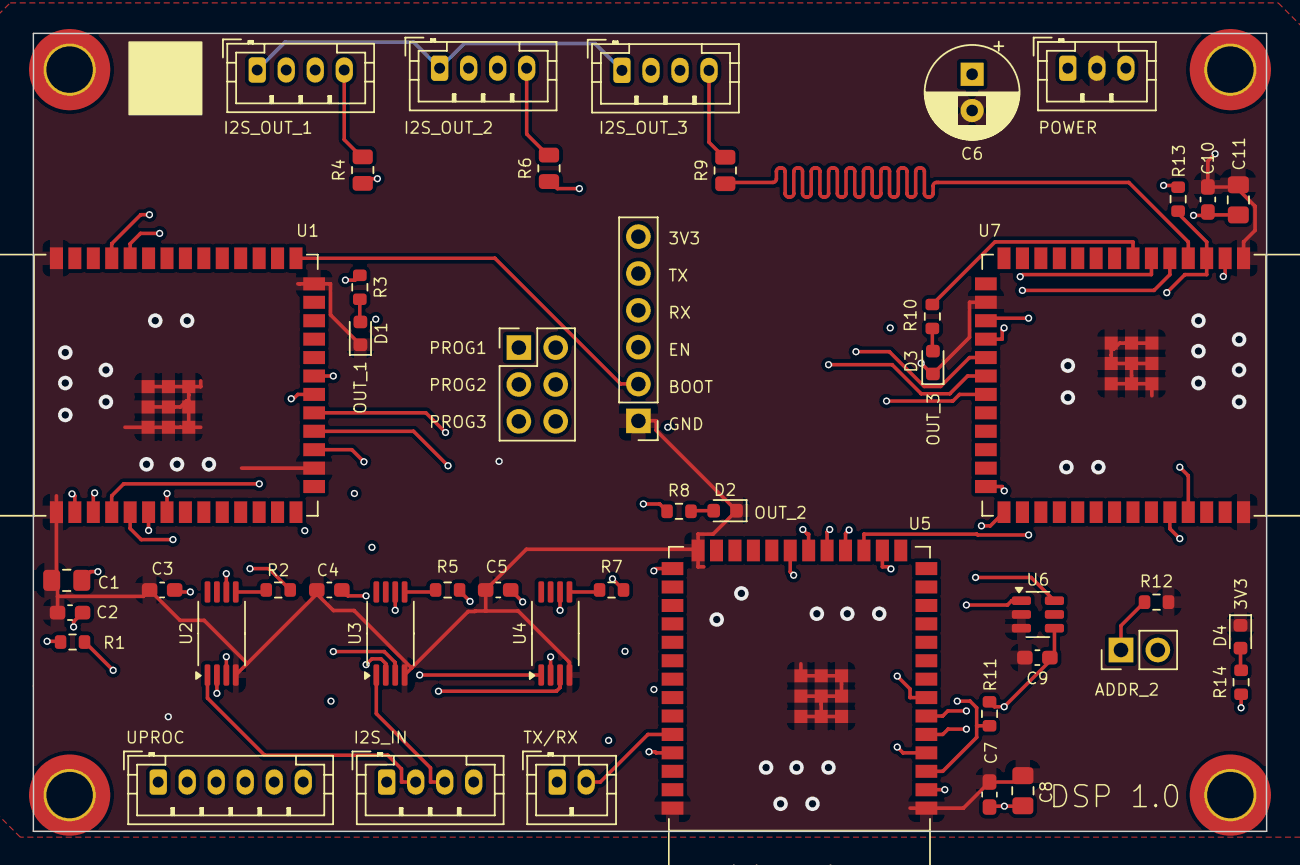
[picture p54: board dsp.kicad_pcb from above]

Board: 4 copper layers, 85.0 x 55.0 mm, 50 parts (0 on the bottom side), 38 nets.
