duanestorey/hifi-amp-pcbs/pcbs/_ready/spdif/_Archived/CS8416/0.1/SPDIF.kicad_pcb

## KiCad design pcbs/_ready/spdif/_Archived/CS8416/0.1/SPDIF.kicad_pcb (2025-01-04, an earlier design)

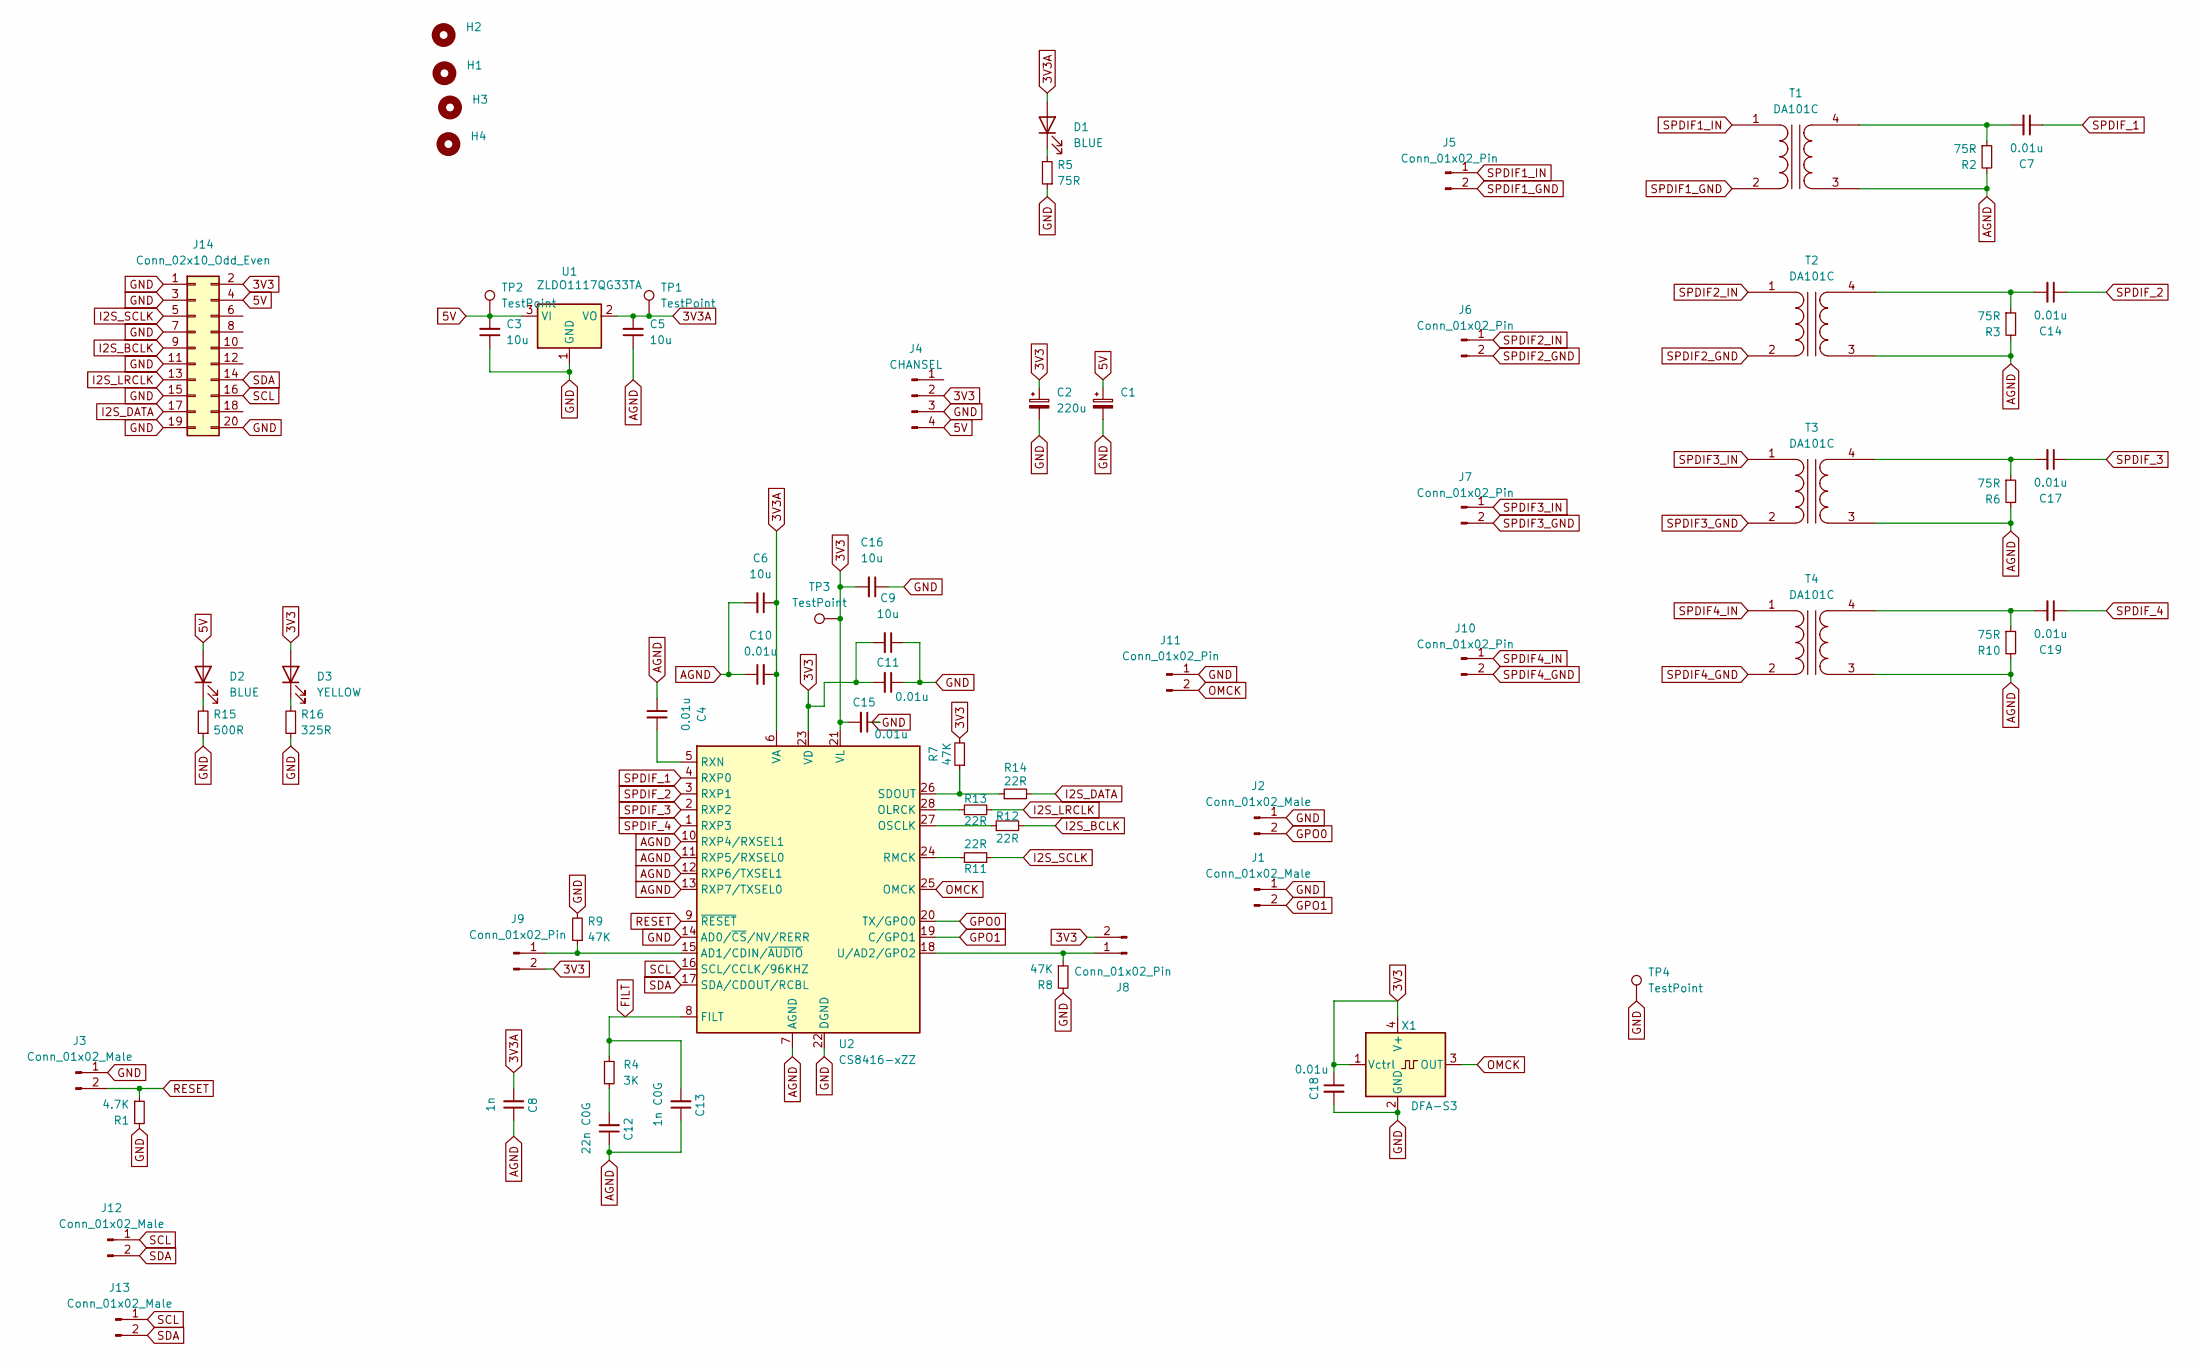
[picture p55: schematic SPDIF.kicad_sch]

Parts:
C1, C2: 220u; CP_Radial_D6.3mm_P2.50mm
C3, C5, C6, C9, C16: 10u; C_1206_3216Metric_Pad1.33x1.80mm_HandSolder
C4, C7, C14, C17, C19: 0.01u; C_0805_2012Metric_Pad1.18x1.45mm_HandSolder
C8: 1n; C_0805_2012Metric_Pad1.18x1.45mm_HandSolder
C10: 0.01u; C_1206_3216Metric_Pad1.33x1.80mm_HandSolder
C11, C15, C18: 0.01u; C_0805_2012Metric
C12: 22n C0G; C_0805_2012Metric_Pad1.18x1.45mm_HandSolder
C13: 1n C0G; C_0805_2012Metric_Pad1.18x1.45mm_HandSolder
D1, D2: BLUE; LED_0805_2012Metric_Pad1.15x1.40mm_HandSolder
D3: YELLOW; LED_0805_2012Metric_Pad1.15x1.40mm_HandSolder
H1, H2, H3, H4: MountingHole; MountingHole_3.2mm_M3
J1, J2, J3, J12, J13: Conn_01x02_Male; JST_PH_B2B-PH-K_1x02_P2.00mm_Vertical
J4: CHANSEL; JST_XH_B4B-XH-A_1x04_P2.50mm_Vertical
J5, J6, J7, J10: Conn_01x02_Pin; JST_XH_B2B-XH-A_1x02_P2.50mm_Vertical
J8, J9, J11: Conn_01x02_Pin; PinHeader_1x02_P2.54mm_Vertical
J14: Conn_02x10_Odd_Even; PinHeader_2x10_P2.54mm_Vertical
R1: 4.7K; R_0603_1608Metric_Pad0.98x0.95mm_HandSolder
R2, R3, R5, R6, R10: 75R; R_0603_1608Metric_Pad0.98x0.95mm_HandSolder
R4: 3K; R_0805_2012Metric_Pad1.20x1.40mm_HandSolder
R7, R8, R9: 47K; R_0603_1608Metric_Pad0.98x0.95mm_HandSolder
R11, R12, R13, R14: 22R; R_1206_3216Metric_Pad1.30x1.75mm_HandSolder
R15: 500R; R_0603_1608Metric_Pad0.98x0.95mm_HandSolder
R16: 325R; R_0603_1608Metric_Pad0.98x0.95mm_HandSolder
T1, T2, T3, T4: DA101C
TP1, TP2, TP3, TP4: TestPoint; TestPoint_THTPad_2.0x2.0mm_Drill1.0mm
U1: ZLDO1117QG33TA; SOT-223-3_TabPin2
U2: CS8416-xZZ; TSSOP-28_4.4x9.7mm_P0.65mm
X1: DFA-S3; Oscillator_SMD_EuroQuartz_XO53-4Pin_5.0x3.2mm_HandSoldering

Connections:
3V3: C2.1, C9.2, C11.2, C15.2, C16.2, C18.1, D3.2 (A), J4.2, J8.2, J9.2, J14.2, R7.2, TP3.1, U2.21 (VL), U2.23 (VD), X1.1 (Vctrl), X1.4 (V+)
3V3A: C5.2, C6.1, C8.2, C10.2, D1.2 (A), TP1.1, U1.2 (VO), U2.6 (VA)
5V: C1.1, C3.2, D2.2 (A), J4.4, J14.4, TP2.1, U1.3 (VI)
AGND: C4.1, C5.1, C6.2, C8.1, C10.1, C12.1, C13.1, R2.2, R3.2, R6.2, R10.2, T1.3 (SA), T2.3 (SA), T3.3 (SA), T4.3 (SA), U2.7 (AGND), U2.10 (RXP4/RXSEL1), U2.11 (RXP5/RXSEL0), U2.12 (RXP6/TXSEL1), U2.13 (RXP7/TXSEL0)
FILT: C13.2, R4.1, U2.8 (FILT)
GND: C1.2, C2.2, C3.1, C9.1, C11.1, C15.1, C16.1, C18.2, J1.1, J2.1, J3.1, J4.3, J11.1, J14.1, J14.3, J14.7, J14.11, J14.15, J14.19, J14.20, R1.2, R5.1, R8.2, R9.2, R15.1, R16.1, TP4.1, U1.1 (GND), U2.14 (AD0/~CS/NV/RERR), U2.22 (DGND), X1.2 (GND)
GPO0: J2.2, U2.20 (TX/GPO0)
GPO1: J1.2, U2.19 (C/GPO1)
I2S_BCLK: J14.9, R12.2
I2S_DATA: J14.17, R14.2
I2S_LRCLK: J14.13, R13.2
I2S_SCLK: J14.5, R11.2
unnamed: C12.2, R4.2
unnamed: D1.1 (K), R5.2
unnamed: D2.1 (K), R15.2
unnamed: D3.1 (K), R16.2
unnamed: J8.1, R8.1, U2.18 (U/AD2/GPO2)
unnamed: J9.1, R9.1, U2.15 (AD1/CDIN/~AUDIO)
unnamed: C7.2, R2.1, T1.4 (SB)
unnamed: C14.2, R3.1, T2.4 (SB)
unnamed: C17.2, R6.1, T3.4 (SB)
unnamed: C19.2, R10.1, T4.4 (SB)
unnamed: R13.1, U2.28 (OLRCK)
unnamed: R12.1, U2.27 (OSCLK)
unnamed: R11.1, U2.24 (RMCK)
unnamed: C4.2, U2.5 (RXN)
unnamed: R7.1, R14.1, U2.26 (SDOUT)
OMCK: J11.2, U2.25 (OMCK), X1.3 (OUT)
RESET: J3.2, R1.1, U2.9 (~RESET)
SCL: J12.1, J13.1, J14.16, U2.16 (SCL/CCLK/96KHZ)
SDA: J12.2, J13.2, J14.14, U2.17 (SDA/CDOUT/RCBL)
SPDIF1_GND: J5.2, T1.2 (AB)
SPDIF1_IN: J5.1, T1.1 (AA)
SPDIF2_GND: J6.2, T2.2 (AB)
SPDIF2_IN: J6.1, T2.1 (AA)
SPDIF3_GND: J7.2, T3.2 (AB)
SPDIF3_IN: J7.1, T3.1 (AA)
SPDIF4_GND: J10.2, T4.2 (AB)
SPDIF4_IN: J10.1, T4.1 (AA)
SPDIF_1: C7.1, U2.4 (RXP0)
SPDIF_2: C14.1, U2.3 (RXP1)
SPDIF_3: C17.1, U2.2 (RXP2)
SPDIF_4: C19.1, U2.1 (RXP3)

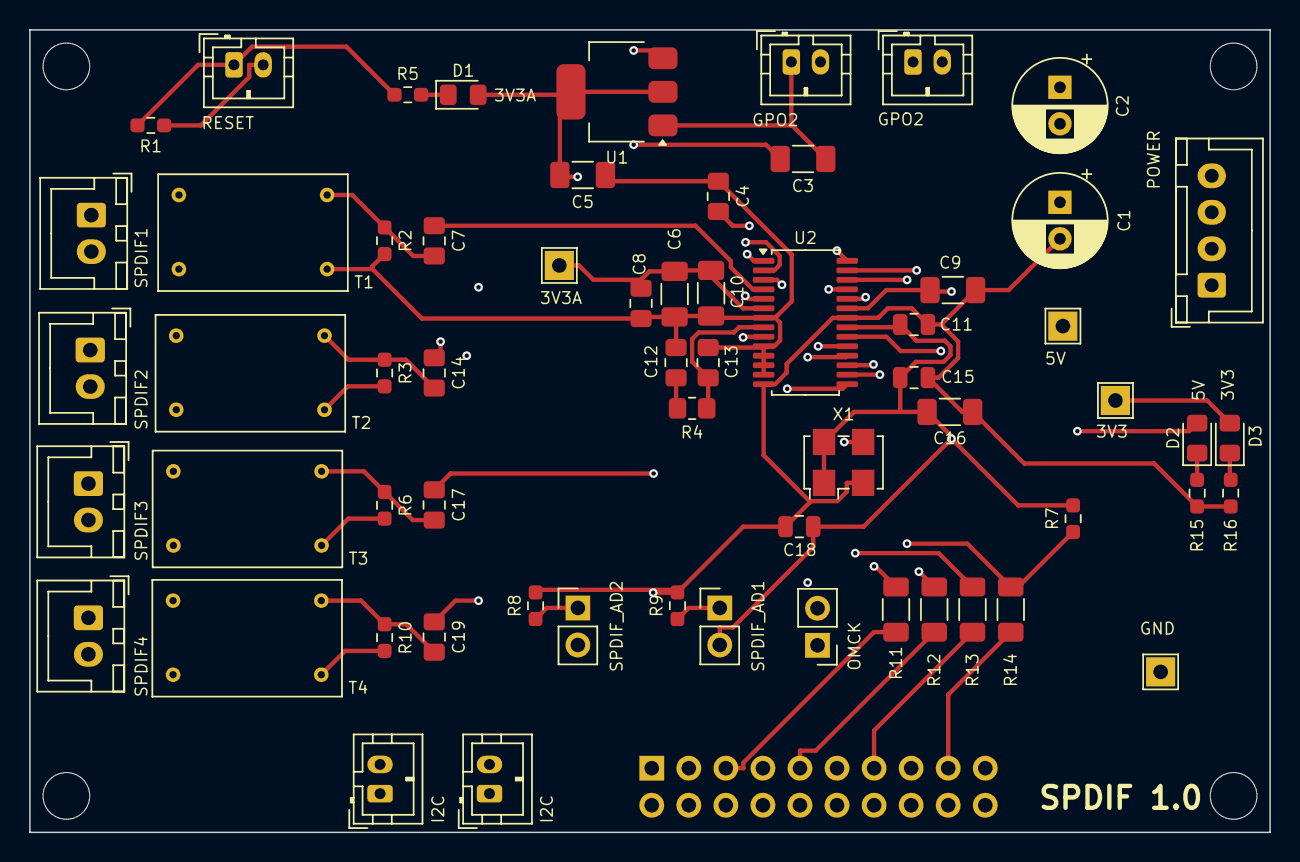
[picture p56: board pcbs/_ready/spdif/_Archived/CS8416/0.1/SPDIF.kicad_pcb from above]

Board: 4 copper layers, 85.0 x 55.0 mm, 67 parts (1 on the bottom side), 43 nets.
