duanestorey/hifi-amp-pcbs/pcbs/_ready/spdif/_Archived/WM8805/0.1/SPDIF.kicad_pcb

## KiCad design pcbs/_ready/spdif/_Archived/WM8805/0.1/SPDIF.kicad_pcb (2025-01-04, an earlier design)

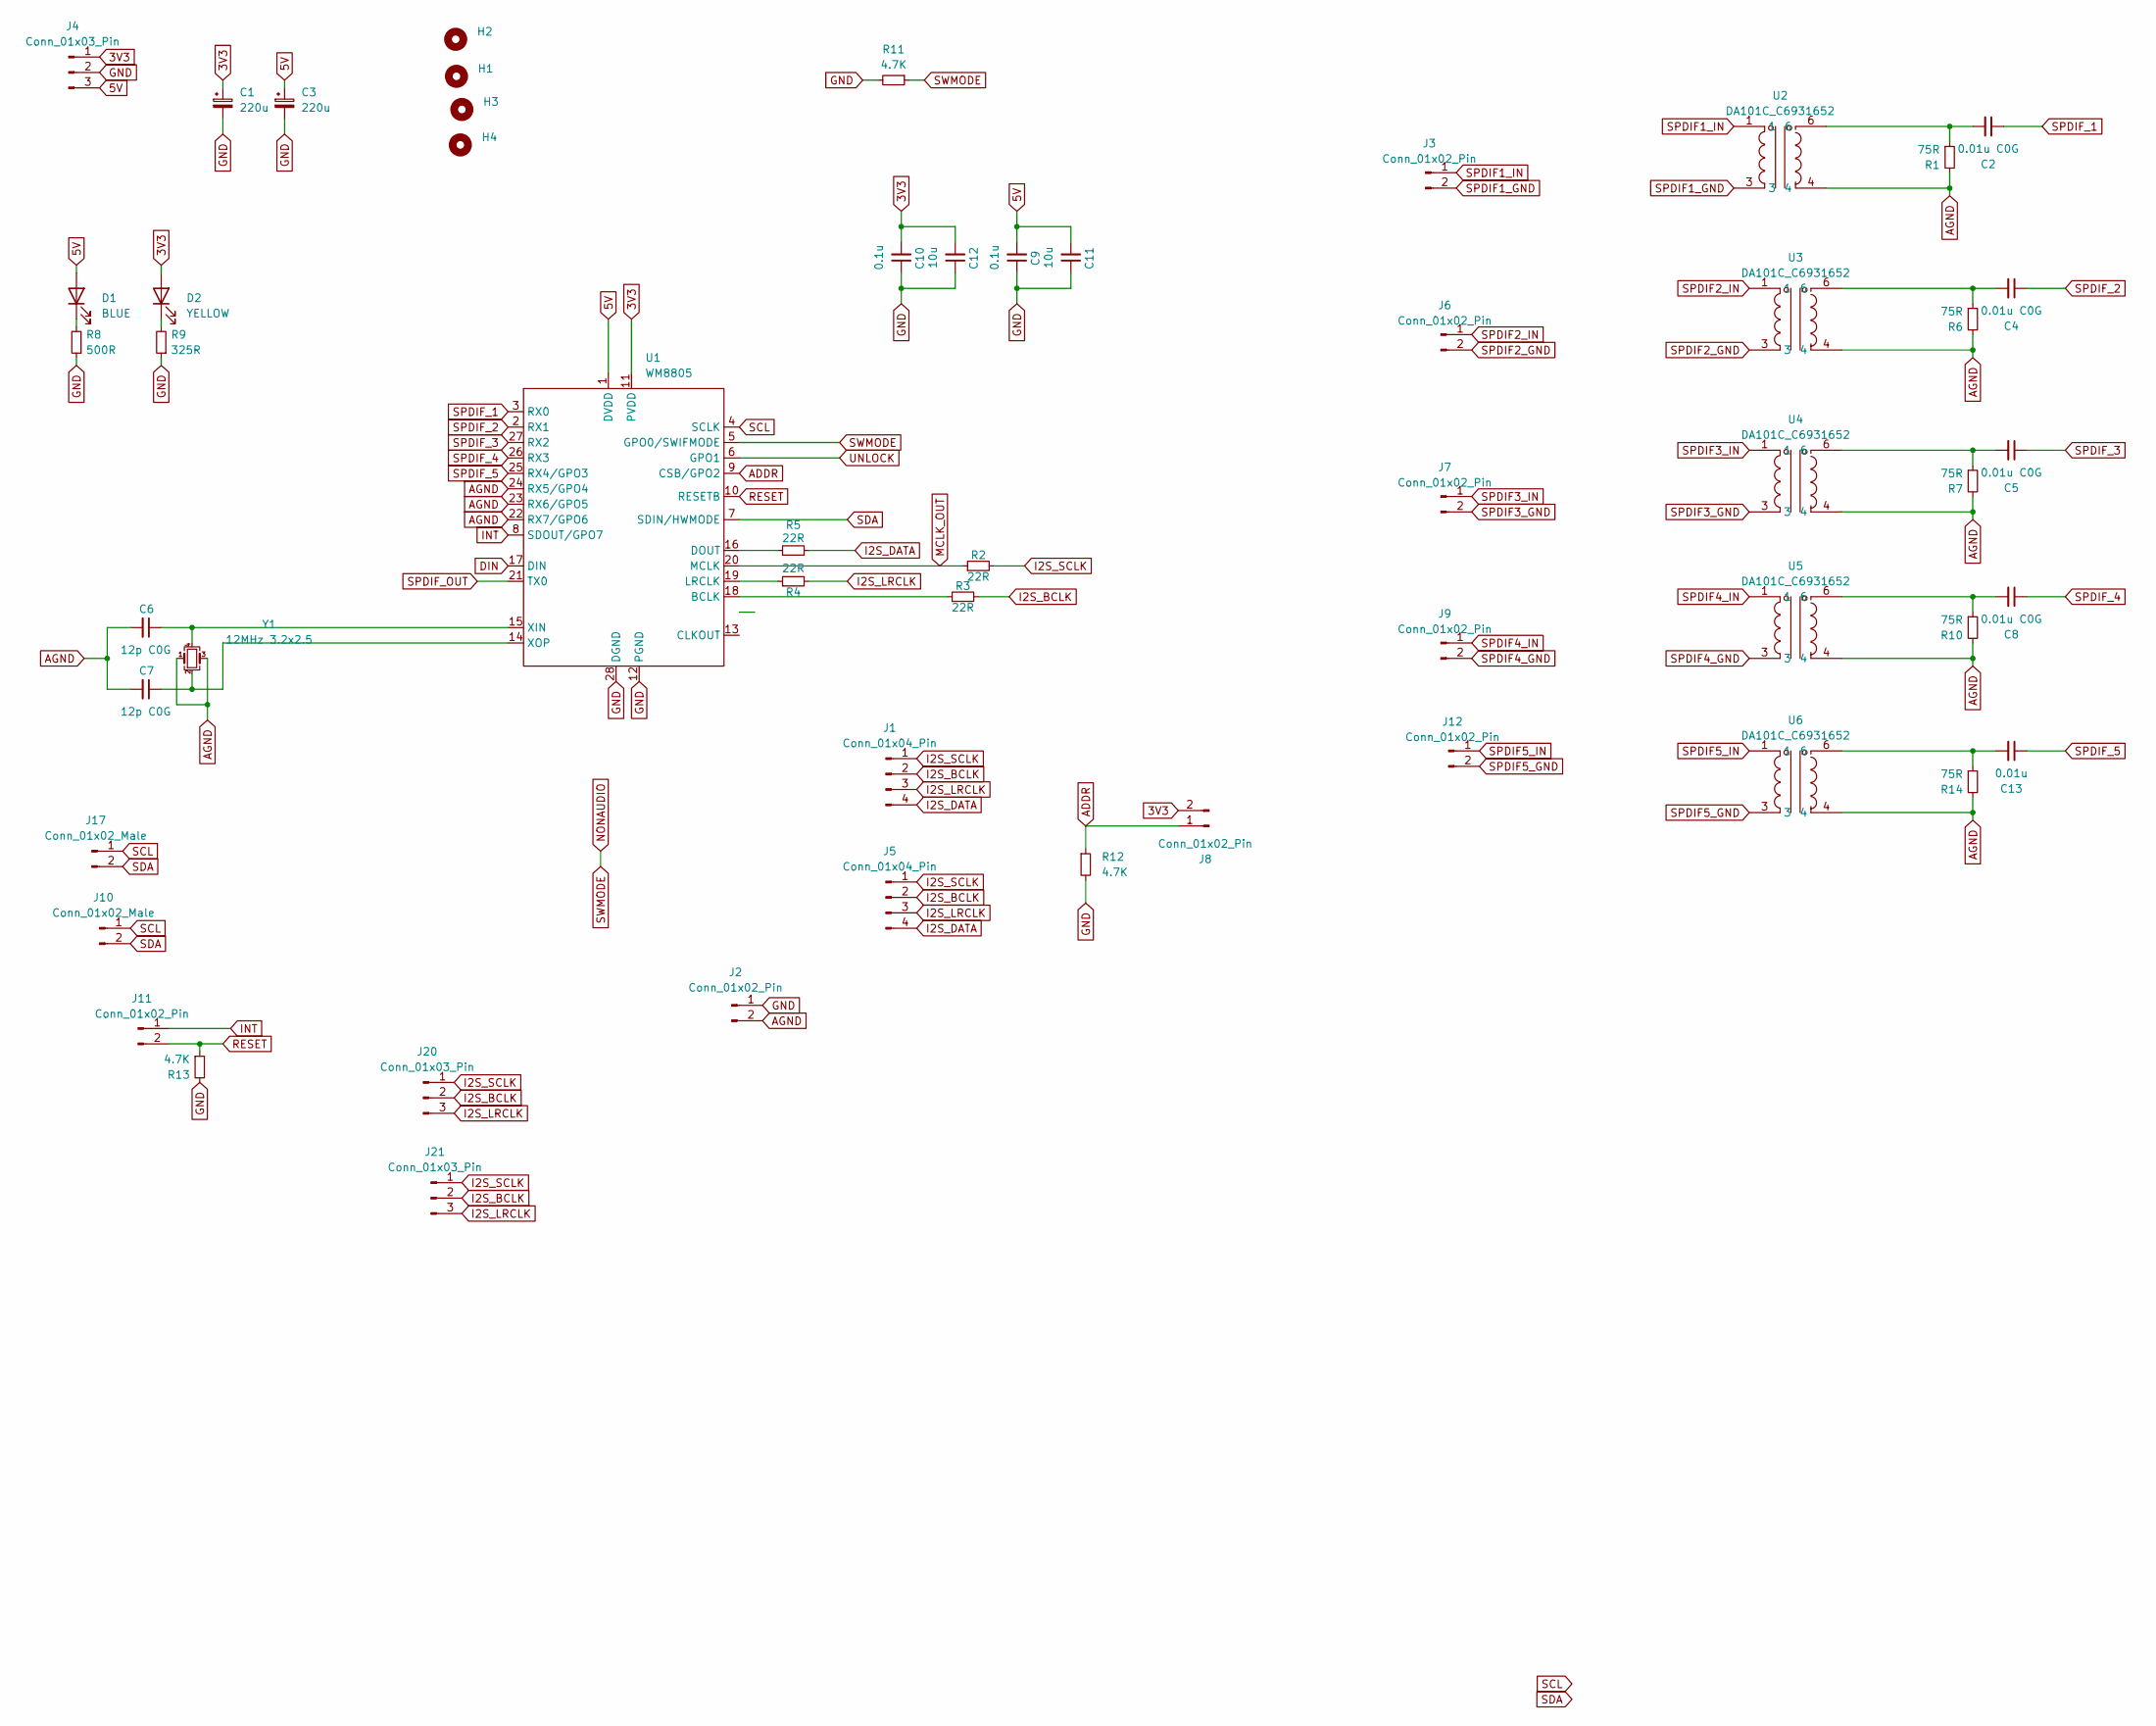
[picture p57: schematic SPDIF.kicad_sch]

Parts:
C1, C3: 220u; CP_Radial_D6.3mm_P2.50mm
C2, C4, C5, C8: 0.01u C0G; C_0805_2012Metric_Pad1.18x1.45mm_HandSolder; Mouser 791-0805N103G250CT
C6, C7: 12p C0G; C_0805_2012Metric_Pad1.18x1.45mm_HandSolder; Mouser 603-CC805FRNPO9BN120
C9, C10: 0.1u; C_0805_2012Metric_Pad1.18x1.45mm_HandSolder
C11, C12: 10u; C_1206_3216Metric_Pad1.33x1.80mm_HandSolder
C13: 0.01u; C_0805_2012Metric_Pad1.18x1.45mm_HandSolder; Mouser C0G
D1: BLUE; LED_0805_2012Metric_Pad1.15x1.40mm_HandSolder
D2: YELLOW; LED_0805_2012Metric_Pad1.15x1.40mm_HandSolder
H1, H2, H3, H4: MountingHole; MountingHole_3.2mm_M3_DIN965_Pad_TopOnly
J1: Conn_01x04_Pin; JST_PH_B4B-PH-K_1x04_P2.00mm_Vertical
J2, J8: Conn_01x02_Pin; PinHeader_1x02_P2.54mm_Vertical
J3, J6, J7, J9, J12: Conn_01x02_Pin; JST_XH_B2B-XH-A_1x02_P2.50mm_Vertical
J4, J20, J21: Conn_01x03_Pin; JST_PH_B3B-PH-K_1x03_P2.00mm_Vertical
J5: Conn_01x04_Pin; PinHeader_1x04_P2.54mm_Vertical
J10, J17: Conn_01x02_Male; JST_PH_B2B-PH-K_1x02_P2.00mm_Vertical
J11: Conn_01x02_Pin; JST_PH_B2B-PH-K_1x02_P2.00mm_Vertical
R1, R6, R7, R10, R14: 75R; R_0603_1608Metric_Pad0.98x0.95mm_HandSolder; Mouser 71-CRCW0603-75-E3
R2, R3, R4, R5: 22R; R_0805_2012Metric_Pad1.20x1.40mm_HandSolder
R8: 500R; R_0603_1608Metric_Pad0.98x0.95mm_HandSolder
R9: 325R; R_0603_1608Metric_Pad0.98x0.95mm_HandSolder
R11, R12, R13: 4.7K; R_0603_1608Metric_Pad0.98x0.95mm_HandSolder
U1: WM8805; SSOP-28_5.3x10.2mm_P0.65mm
U2, U3, U4, U5, U6: DA101C_C6931652; XFMR-TH_4P-L9.5-W9.0-P5.08-LS10.2_C9900096976; LCSC Part C6931652
Y1: 12MHz 3.2x2.5; Crystal_SMD_SeikoEpson_FA238-4Pin_3.2x2.5mm; Mouser 520-120-8-33B2CKMTR3

Connections:
3V3: C1.1, C10.2, C12.2, D2.2 (A), J4.1, J8.2, U1.11 (PVDD)
5V: C3.1, C9.2, C11.2, D1.2 (A), J4.3, U1.1 (DVDD)
ADDR: J8.1, R12.1, U1.9 (CSB/GPO2)
AGND: C6.2, C7.2, J2.2, R1.2, R6.2, R7.2, R10.2, R14.2, U1.22 (RX7/GPO6), U1.23 (RX6/GPO5), U1.24 (RX5/GPO4), U2.4, U3.4, U4.4, U5.4, U6.4, Y1.1, Y1.3
DIN: U1.17 (DIN)
GND: C1.2, C3.2, C9.1, C10.1, C11.1, C12.1, J2.1, J4.2, R8.1, R9.1, R11.2, R12.2, R13.2, U1.12 (PGND), U1.28 (DGND)
I2S_BCLK: J1.2, J5.2, J20.2, J21.2, R3.2
I2S_DATA: J1.4, J5.4, R5.2
I2S_LRCLK: J1.3, J5.3, J20.3, J21.3, R4.2
I2S_SCLK: J1.1, J5.1, J20.1, J21.1, R2.2
INT: J11.1, U1.8 (SDOUT/GPO7)
MCLK_OUT: R2.1, U1.20 (MCLK)
NONAUDIO: R11.1, U1.5 (GPO0/SWIFMODE)
unnamed: C2.2, R1.1, U2.6
unnamed: C4.2, R6.1, U3.6
unnamed: C5.2, R7.1, U4.6
unnamed: C8.2, R10.1, U5.6
unnamed: C13.2, R14.1, U6.6
unnamed: D1.1 (K), R8.2
unnamed: D2.1 (K), R9.2
unnamed: R3.1, U1.18 (BCLK)
unnamed: R5.1, U1.16 (DOUT)
unnamed: R4.1, U1.19 (LRCLK)
unnamed: C6.1, U1.15 (XIN), Y1.4
unnamed: C7.1, U1.14 (XOP), Y1.2
RESET: J11.2, R13.1, U1.10 (RESETB)
SCL: J10.1, J17.1, U1.4 (SCLK)
SDA: J10.2, J17.2, U1.7 (SDIN/HWMODE)
SPDIF1_GND: J3.2, U2.3
SPDIF1_IN: J3.1, U2.1
SPDIF2_GND: J6.2, U3.3
SPDIF2_IN: J6.1, U3.1
SPDIF3_GND: J7.2, U4.3
SPDIF3_IN: J7.1, U4.1
SPDIF4_GND: J9.2, U5.3
SPDIF4_IN: J9.1, U5.1
SPDIF5_GND: J12.2, U6.3
SPDIF5_IN: J12.1, U6.1
SPDIF_1: C2.1, U1.3 (RX0)
SPDIF_2: C4.1, U1.2 (RX1)
SPDIF_3: C5.1, U1.27 (RX2)
SPDIF_4: C8.1, U1.26 (RX3)
SPDIF_5: C13.1, U1.25 (RX4/GPO3)
SPDIF_OUT: U1.21 (TX0)
UNLOCK: U1.6 (GPO1)

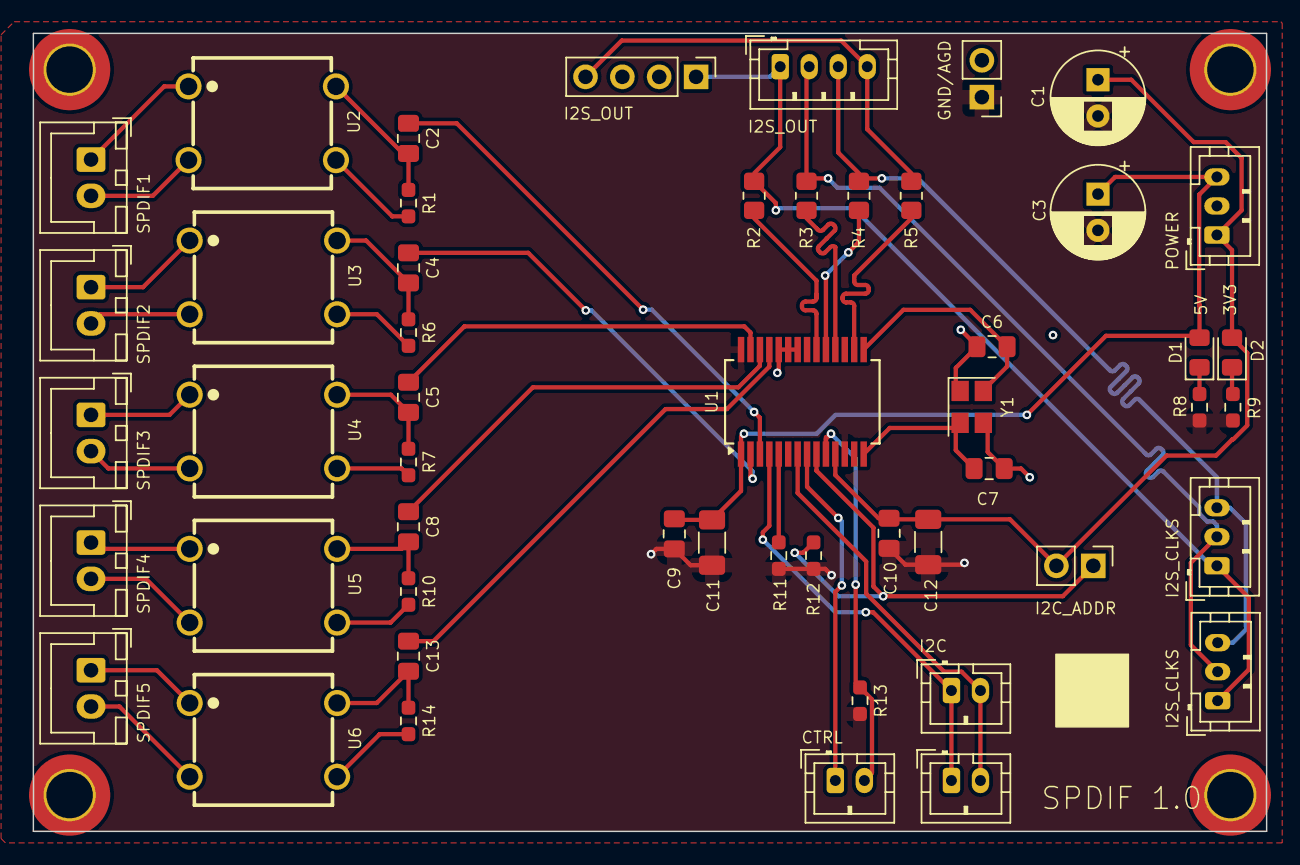
[picture p58: board pcbs/_ready/spdif/_Archived/WM8805/0.1/SPDIF.kicad_pcb from above]

Board: 4 copper layers, 85.0 x 55.0 mm, 55 parts (0 on the bottom side), 42 nets.
