duanestorey/hifi-amp-pcbs/pcbs/plate-amp/1.0/plate-amp.kicad_pcb

## KiCad design pcbs/plate-amp/1.0/plate-amp.kicad_pcb (2025-01-09)

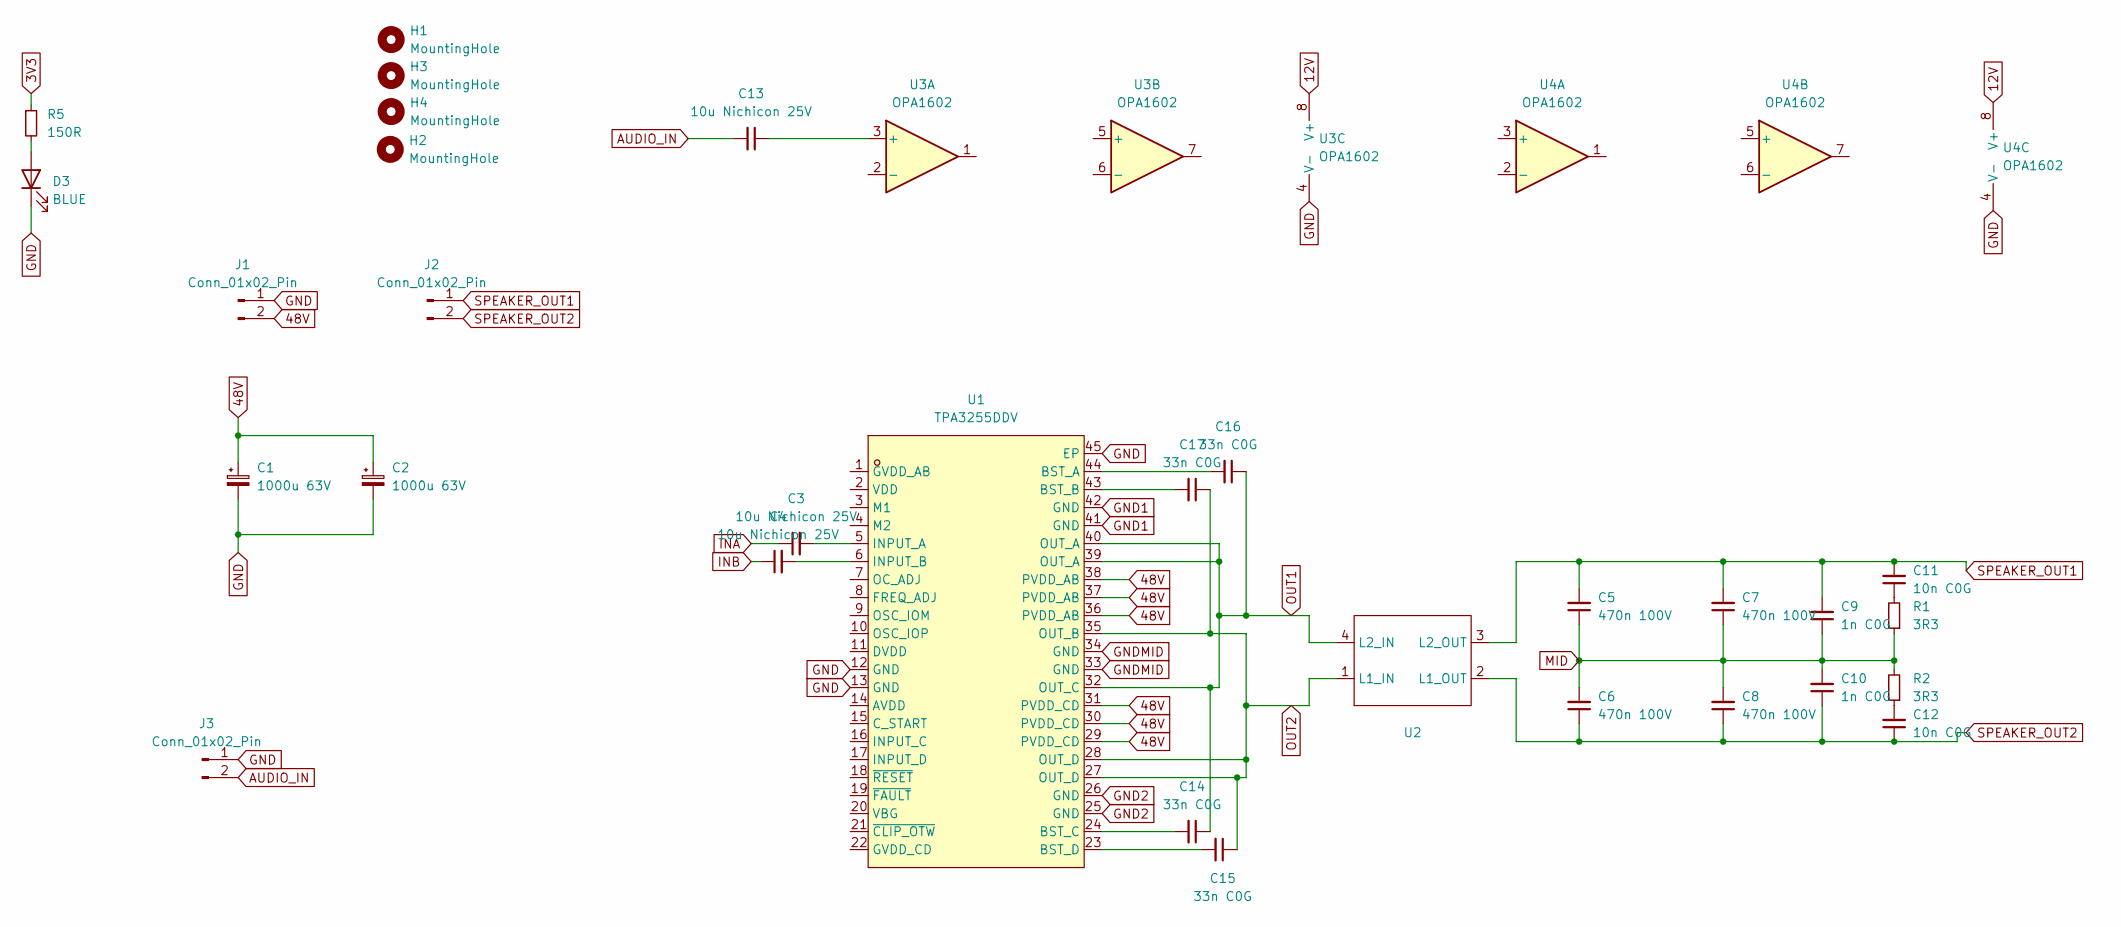
[picture p59: schematic plate-amp.kicad_sch]

Parts:
C1, C2: 1000u 63V; CP_Radial_D16.0mm_P7.50mm
C3, C4, C13: 10u Nichicon 25V; CP_Radial_D5.0mm_P2.50mm
C5, C6, C7, C8: 470n 100V; C_Rect_L18.0mm_W9.0mm_P15.00mm_FKS3_FKP3
C9, C10: 1n C0G; C_1206_3216Metric
C11, C12: 10n C0G; C_1206_3216Metric
C14, C15, C16, C17: 33n C0G; C_0805_2012Metric
D3: BLUE; LED_0603_1608Metric_Pad1.05x0.95mm_HandSolder; LCSC XL-1608UBC-04
H1, H2, H3, H4: MountingHole; MountingHole_3.2mm_M3_DIN965_Pad_TopOnly
J1, J2: Conn_01x02_Pin; JST_VH_B2P-VH-B_1x02_P3.96mm_Vertical
J3: Conn_01x02_Pin; JST_PH_B2B-PH-K_1x02_P2.00mm_Vertical
R1, R2: 3R3; R_2010_5025Metric_Pad1.40x2.65mm_HandSolder
R5: 150R; R_0603_1608Metric_Pad0.98x0.95mm_HandSolder
U1: TPA3255DDV; HTSSOP-44_L14.0-W6.1-P0.64-LS8.1-BL-EP; LCSC Part C2879299
U2: UA8014-AL
U3, U4: OPA1602; SOIC-8_3.9x4.9mm_P1.27mm

Connections:
3V3: R5.1
12V: U3.8 (V+), U4.8 (V+)
48V: C1.1, C2.1, J1.2, U1.29 (PVDD_CD), U1.30 (PVDD_CD), U1.31 (PVDD_CD), U1.36 (PVDD_AB), U1.37 (PVDD_AB), U1.38 (PVDD_AB)
AUDIO_IN: C13.2, J3.2
GND: C1.2, C2.2, D3.1 (K), J1.1, J3.1, U1.12 (GND), U1.13 (GND), U1.45 (EP), U3.4 (V-), U4.4 (V-)
GND1: U1.41 (GND), U1.42 (GND)
GND2: U1.25 (GND), U1.26 (GND)
GNDMID: U1.33 (GND), U1.34 (GND)
INA: C3.1
INB: C4.1
MID: C5.1, C6.2, C7.1, C8.2, C9.1, C10.2, R1.1, R2.2
unnamed: C11.1, R1.2
unnamed: C12.2, R2.1
unnamed: D3.2 (A), R5.2
unnamed: C16.2, U1.44 (BST_A)
unnamed: C17.2, U1.43 (BST_B)
unnamed: C14.2, U1.24 (BST_C)
unnamed: C15.2, U1.23 (BST_D)
unnamed: C3.2, U1.5 (INPUT_A)
unnamed: C4.2, U1.6 (INPUT_B)
unnamed: C13.1, U3.3 (+)
OUT1: C14.1, C16.1, U1.32 (OUT_C), U1.39 (OUT_A), U1.40 (OUT_A), U2.4 (L2_IN)
OUT2: C15.1, C17.1, U1.27 (OUT_D), U1.28 (OUT_D), U1.35 (OUT_B), U2.1 (L1_IN)
SPEAKER_OUT1: C5.2, C7.2, C9.2, C11.2, J2.1, U2.3 (L2_OUT)
SPEAKER_OUT2: C6.1, C8.1, C10.1, C12.1, J2.2, U2.2 (L1_OUT)

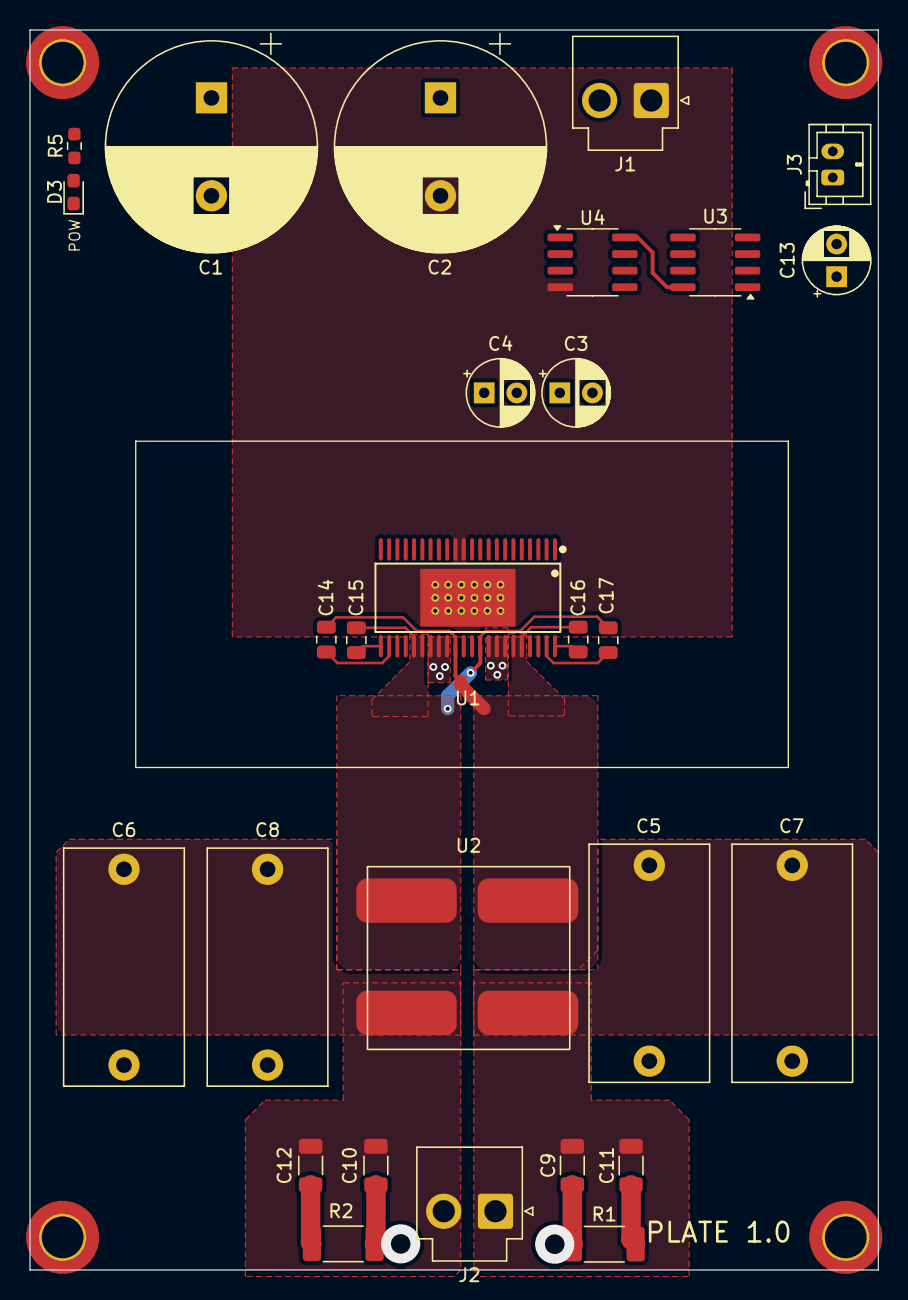
[picture p60: board plate-amp.kicad_pcb from above]

Board: 2 copper layers, 65.0 x 95.0 mm, 32 parts (0 on the bottom side), 22 nets.
